juanlugo456/GRUPO-FUNBIO/Talleres/T2/T1 (1).docx

Medición | Valor (V)
1 | 5.063
2 | 5.065
3 | 5.069
4 | 5.070
5 | 5.070
6 | 5.046
7 | 5.018
8 | 5.062
9 | 5.063
10 | 5.027
Promedio | 5.0551
Ea | 0.0551
Er | 0.01102
Medición Valor (V) 1 3.354 2 3.360 3 3.300 4 3.342 5 3.301 6 3.362 7 3.294 8 3.365 9 3.320 10 3.279 Promedio 3.3277 Ea 0.0277 Er 8.39 × 10⁻³ Medición Valor (V) 1 12.03 2 12.05 3 12.02 4 12.07 5 12.00 6 12.04 7 12.03 8 12.06 9 11.99 10 12.06 Promedio 12.035 Ea 0.035 Er 2.92 × 10⁻³

Voltaje Nominal | Promedio Medido (V) | Error Absoluto Medio (Ea) | Error Relativo Medio (Er)
5 V | 5.0551 | 0.0551 | 0.01102
3.3 V | 3.3277 | 0.0277 | 8.39 × 10⁻³
12 V | 12.035 | 0.035 | 2.92 × 10⁻³
