juanlugo456/GRUPO-FUNBIO/Entregable/Entregable 8.pdf

# Entregable 8 - Grupo 3

# Fundamentos de Biodiseño

# Integrantes:

## Juan Carlos Lugo Lorena Mendez Nathalie Huiza Ignacio Pérez Fabio García Jean Neira

2025

## 1.- Diagrama o Esquema Electrónico

## -Actuador:

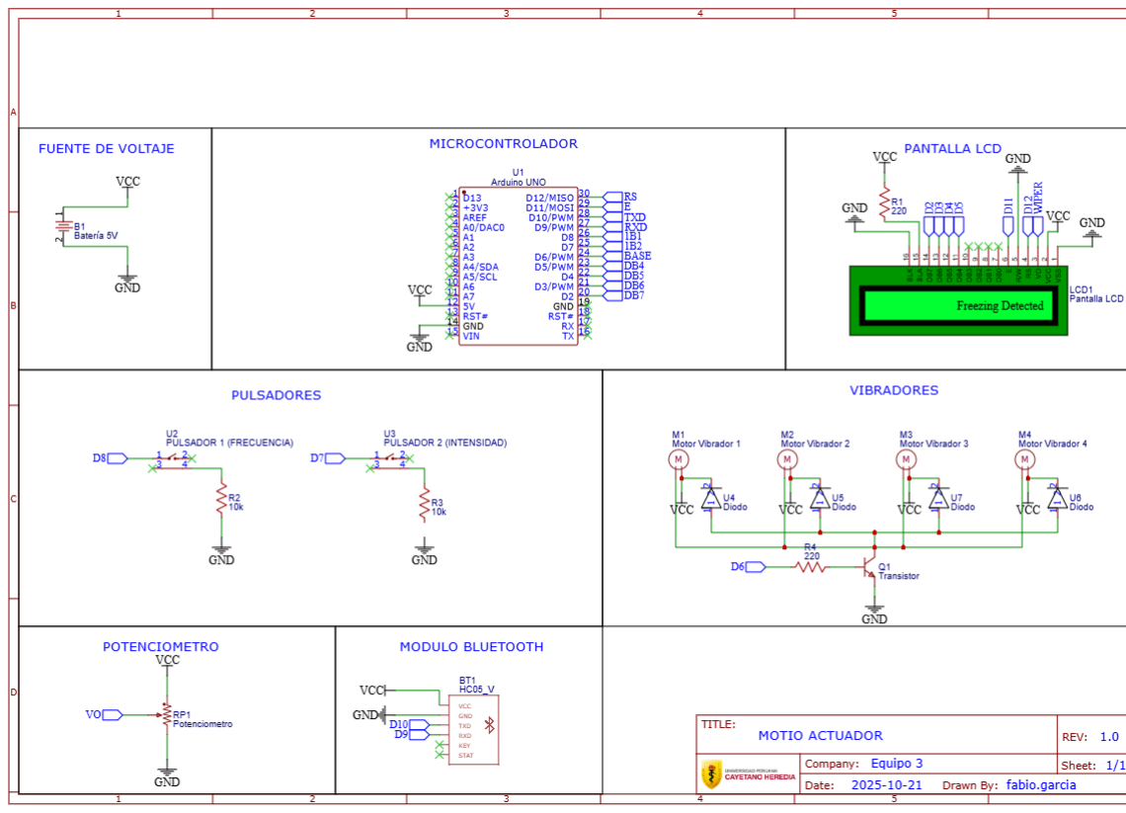
[picture p24: figure]

## -Detector

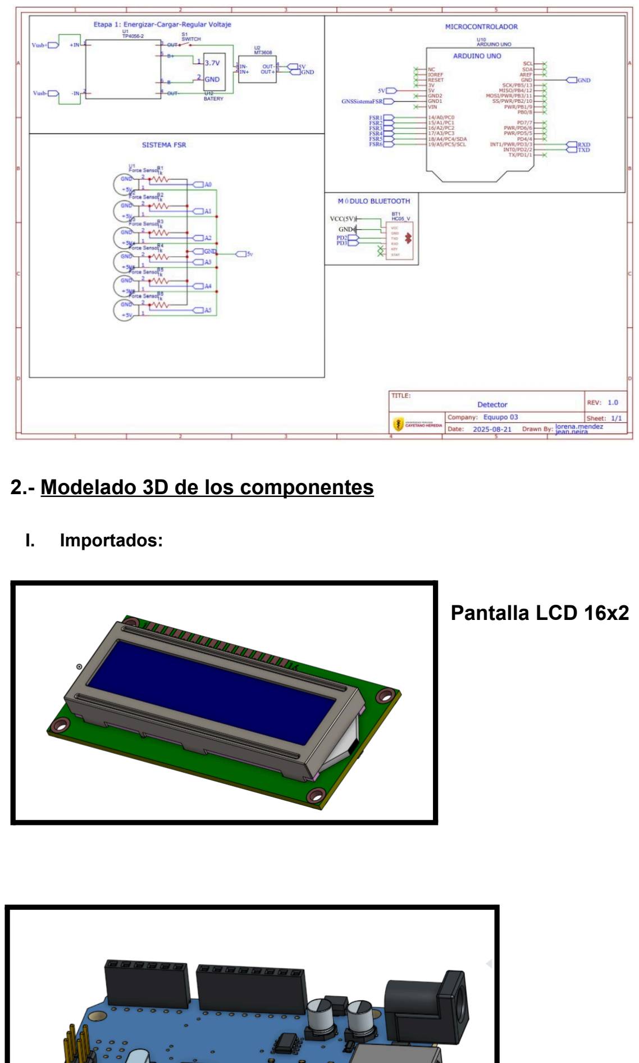
[picture p25: page 3]

## 2.- Modelado 3D de los componentes

I. Importados:

## Pantalla LCD 16x2

## Arduino Uno

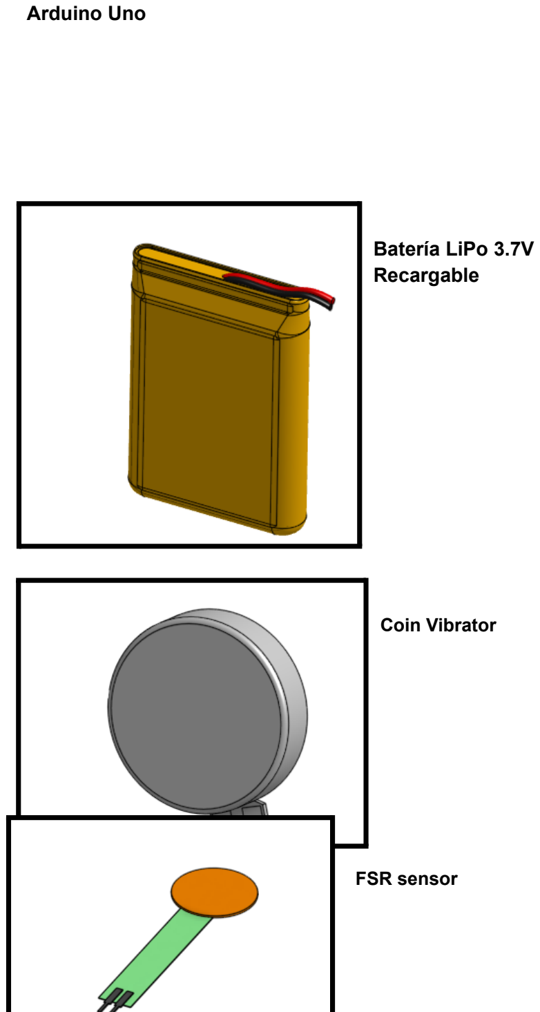
[picture p26: page 4]

## Batería LiPo 3.7V Recargable

### Coin Vibrator

### FSR sensor

## Botón

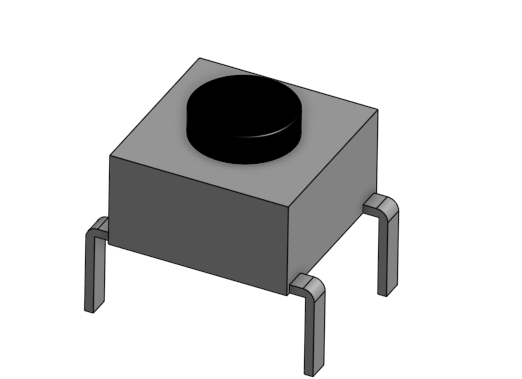
[picture p27: figure]

## II. Modelados:

## Plantilla

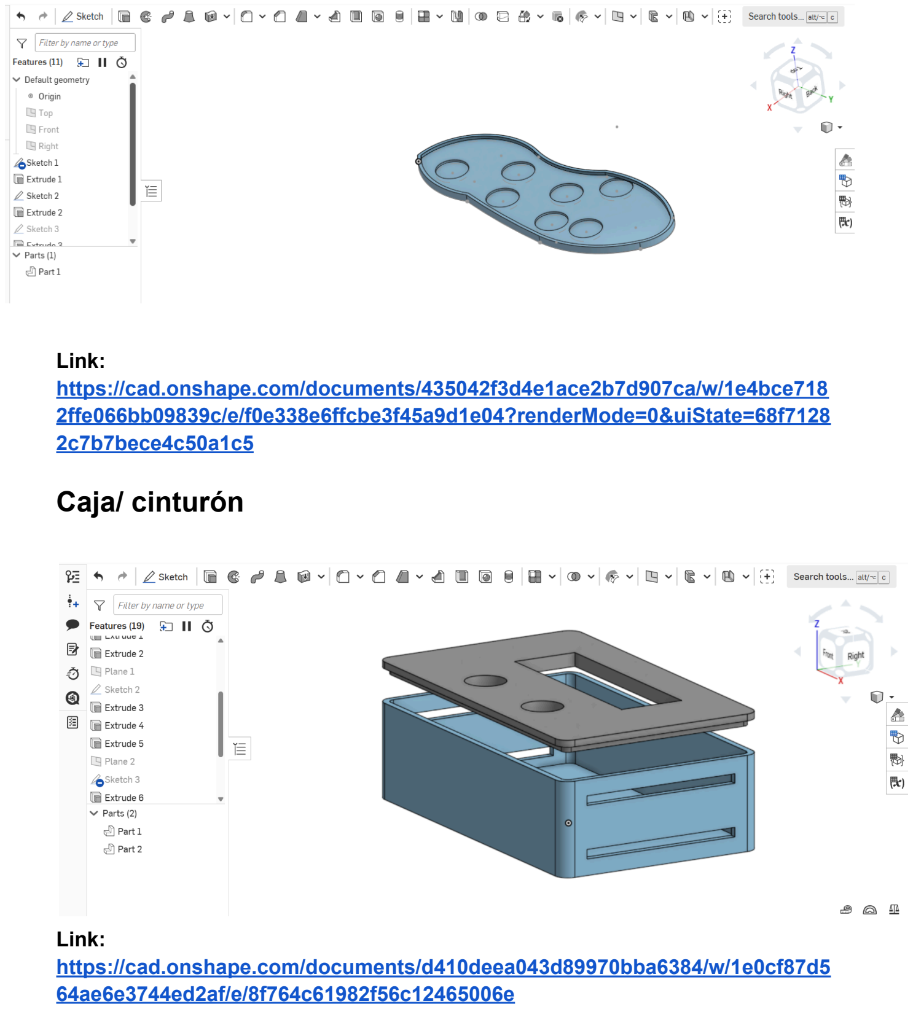
[picture p28: page 6]

Link:
https://cad.onshape.com/documents/435042f3d4e1ace2b7d907ca/w/1e4bce7182ffe066bb09839c/e/f0e338e6ffcbe3f45a9d1e04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 2c7b7bece4c50a1c5 (https://cad.onshape.com/documents/435042f3d4e1ace2b7d907ca/w/1e4bce7182ffe066bb09839c/e/f0e338e6ffcbe3f45a9d1e04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)

## Caja/ cinturón

Link:
https://cad.onshape.com/documents/d410deea043d89970bba6384/w/1e0cf87d564ae6e3744ed2af/e/8f764c61982f56c12465006e (https://cad.onshape.com/documents/d410deea043d89970bba6384/w/1e0cf87d564ae6e3744ed2af/e/8f764c61982f56c12465006e)
