juanlugo456/GRUPO-FUNBIO/Talleres/T8/lorena-mendez-certificate.pdf

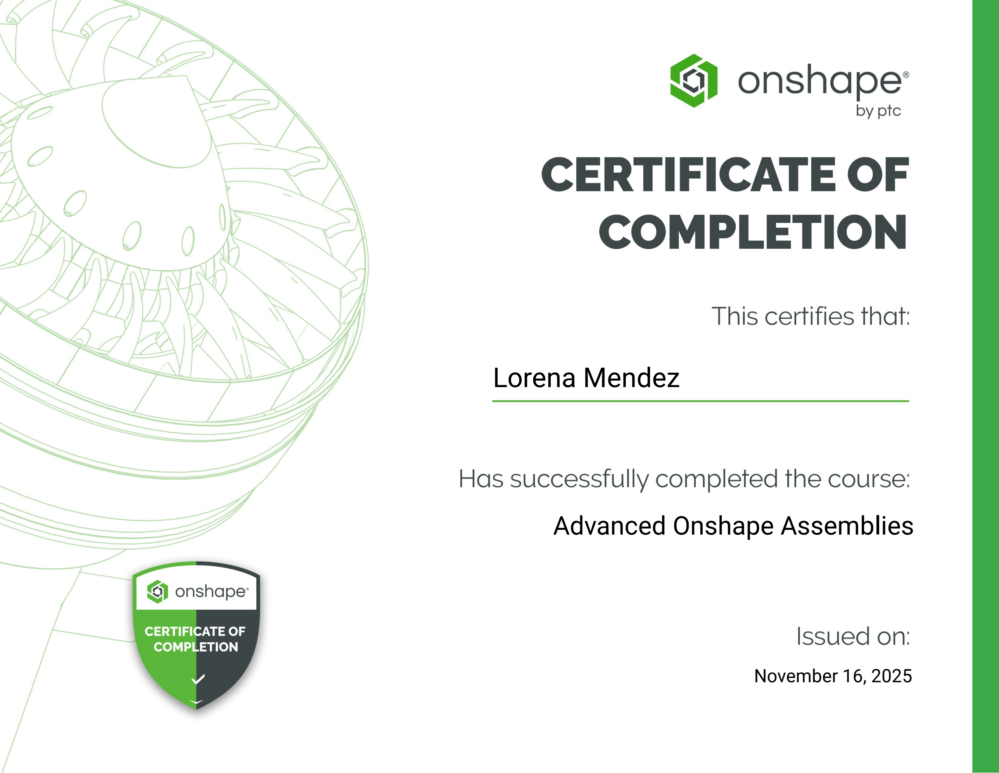
[picture p29: page 1]

Lorena Mendez

Advanced Onshape Assemblies

November 16, 2025
