juanlugo456/GRUPO-FUNBIO/Talleres/T8/Taller 8 certificado Ignacio Pérez.pdf

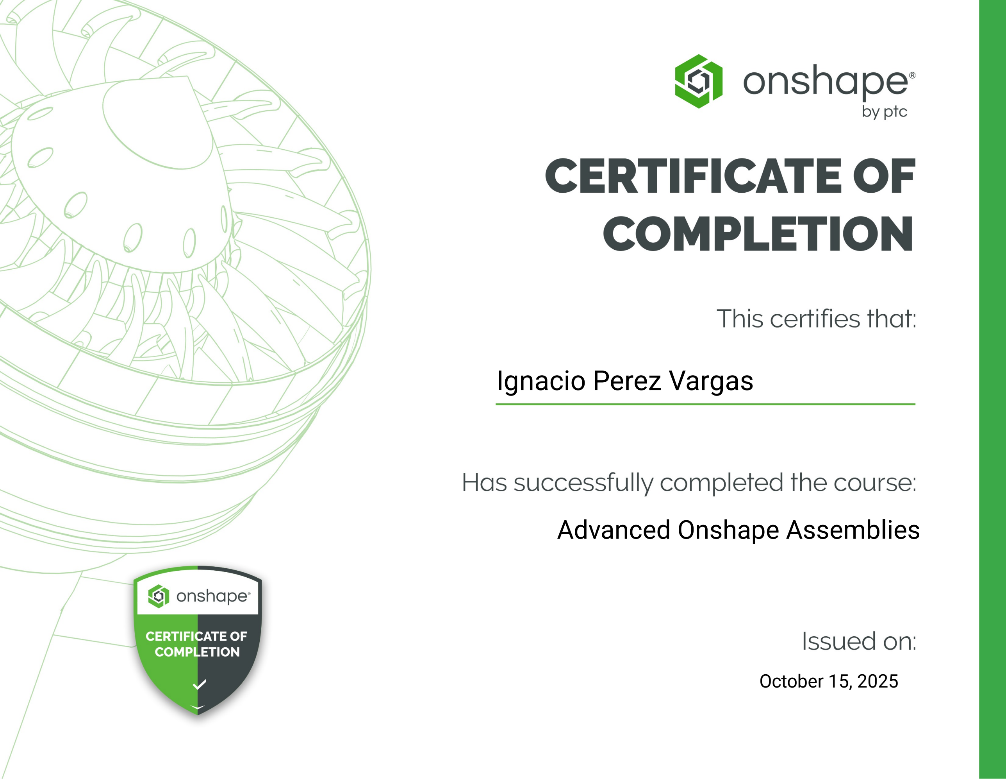
[picture p30: page 1]

Ignacio Perez Vargas

Advanced Onshape Assemblies

October 15, 2025
