juanlugo456/GRUPO-FUNBIO/Talleres/T8/fabio-ivan-garcia-soto-032f19d1-8f02-4be0-8b31-2a58900b8acc-certificate (1).pdf

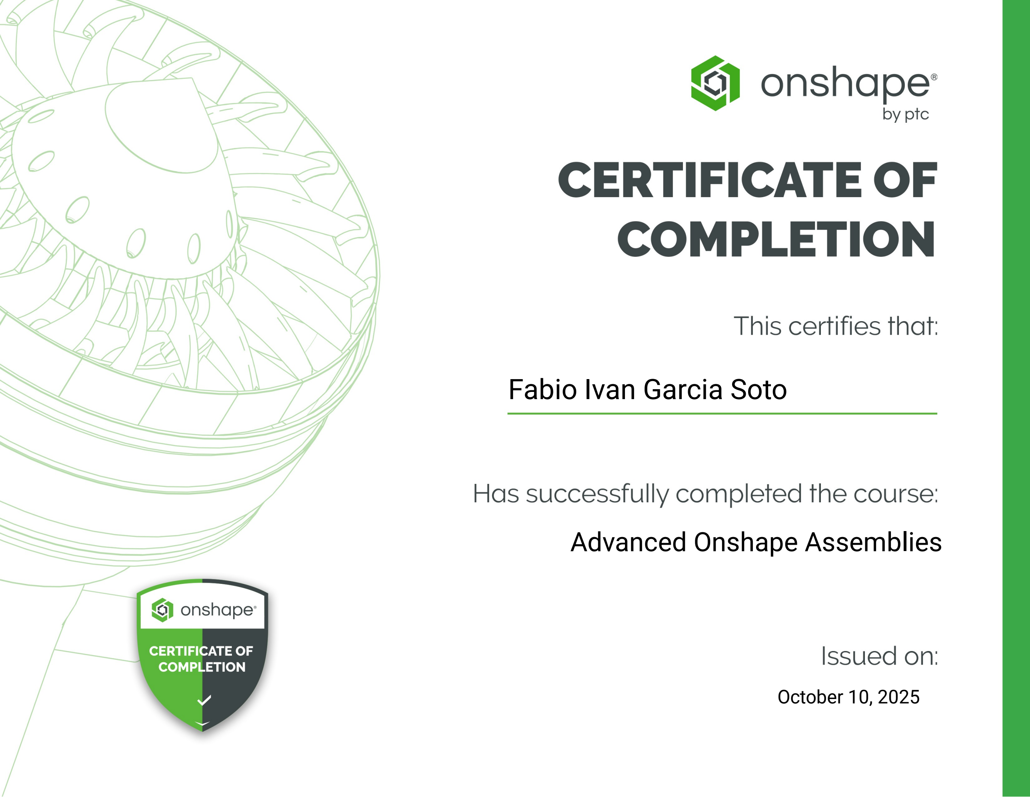
[picture p31: page 1]

Fabio Ivan Garcia Soto

Advanced Onshape Assemblies

October 10, 2025
