juanlugo456/GRUPO-FUNBIO/Talleres/T8/LUGO RODRIGUEZ JUAN CARLOS -taller 8.pdf

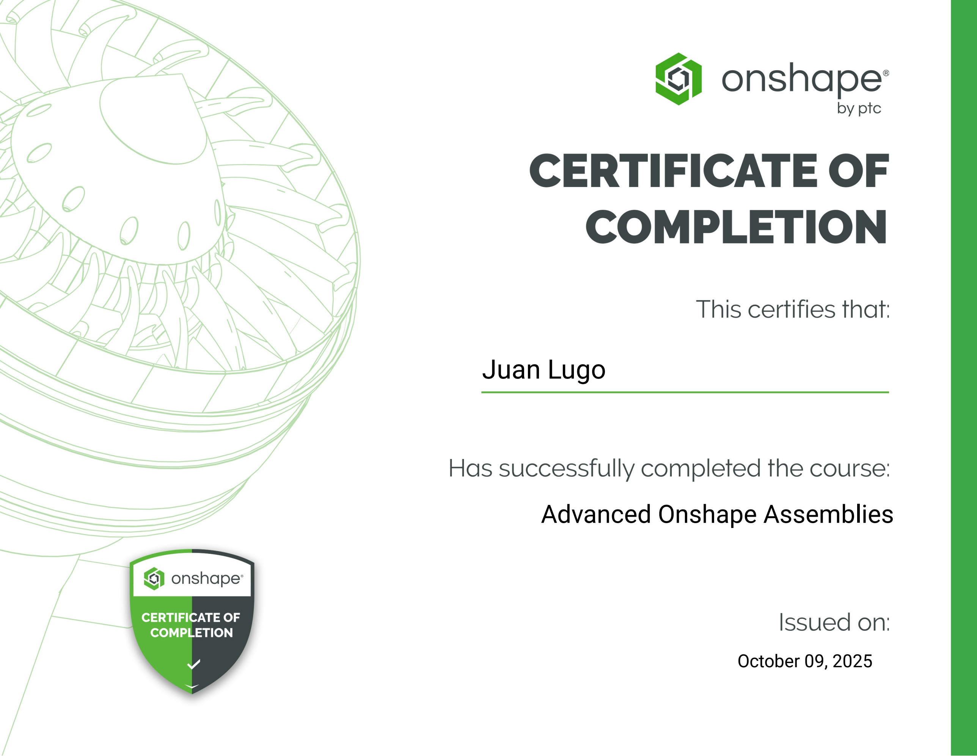
[picture p32: page 1]

Juan Lugo

Advanced Onshape Assemblies

October 09, 2025
