juanlugo456/GRUPO-FUNBIO/Talleres/T8/Nathalie Huiza certificado.pdf

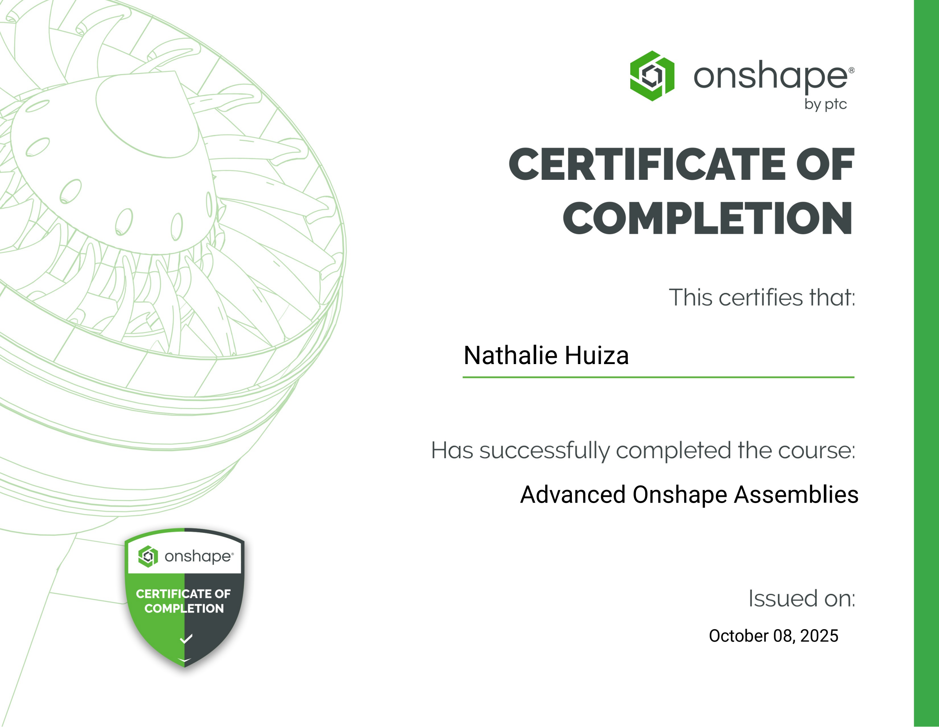
[picture p33: page 1]

Nathalie Huiza

Advanced Onshape Assemblies

October 08, 2025
