juanlugo456/GRUPO-FUNBIO/Talleres/T6/Certificados- Juan Carlos Lugo Rodriguez.pdf

Juan Lugo

September 20, 2025

Onshape Assemblies

Juan Lugo

September 20, 2025

Detailed Drawings

Juan Lugo

September 20, 2025

Multi-Part Part Studios

Juan Lugo

Introduction to Part Studios

September 20, 2025

Juan Lugo

Introduction to Sketching

September 20, 2025
