juanlugo456/GRUPO-FUNBIO/Talleres/T6/Nathalie Antonella Huiza Quispe_C.O.pdf

Nathalie Huiza

Introduction to Sketching

September 17, 2025

Nathalie Huiza

Introduction to Part Studios

September 19, 2025

Nathalie Huiza

September 19, 2025

Multi-Part Part Studios

Nathalie Huiza

September 19, 2025

Onshape Assemblies

Nathalie Huiza

September 19, 2025

Detailed Drawings
