juanlugo456/GRUPO-FUNBIO/Talleres/T2/T2 Resistencias en Protoboard.docx

Pollo

Horizontal

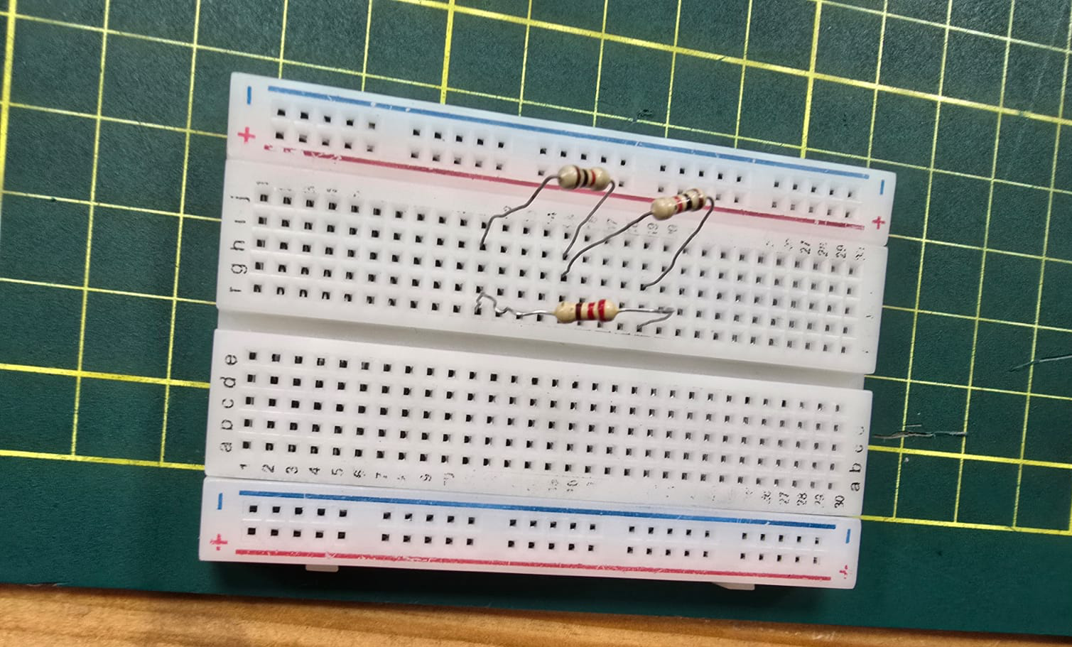
[picture p54: figure]

Vertical

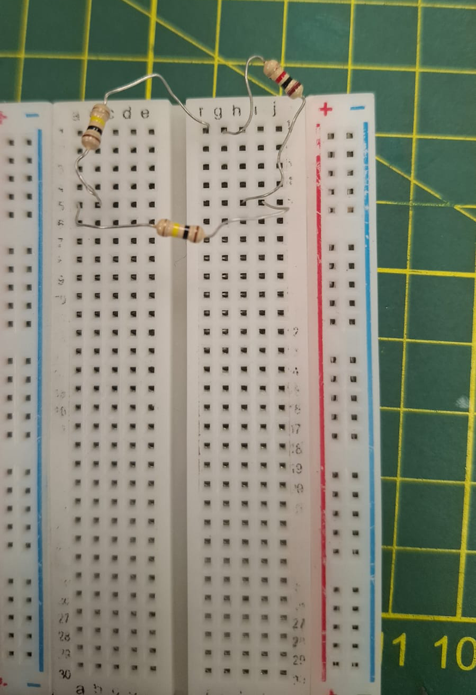
[picture p55: figure]

Gato

Horizontal

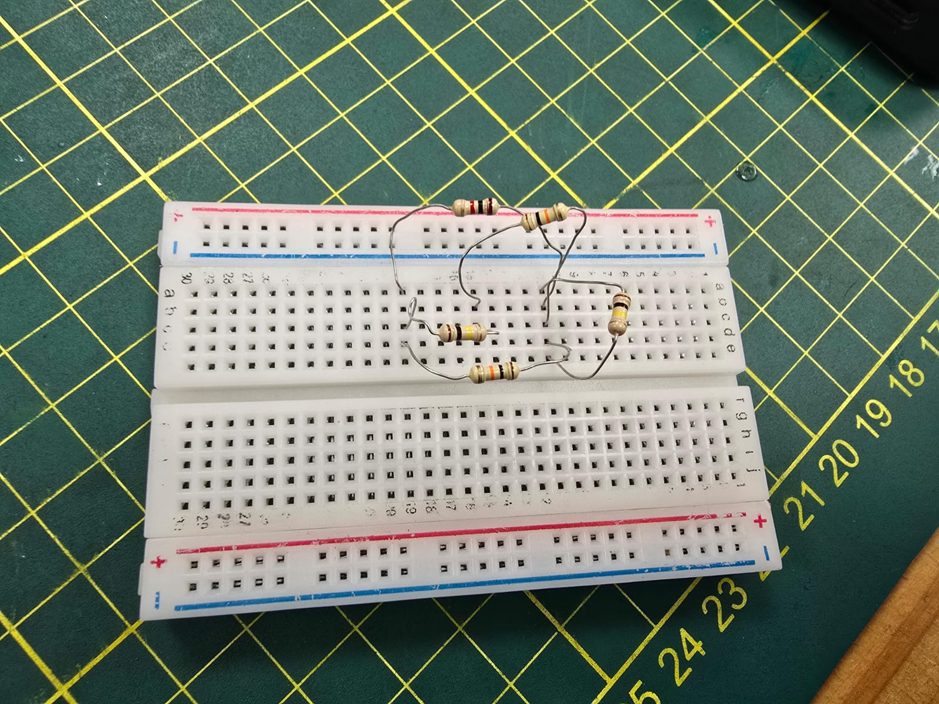
[picture p56: figure]

Vertical

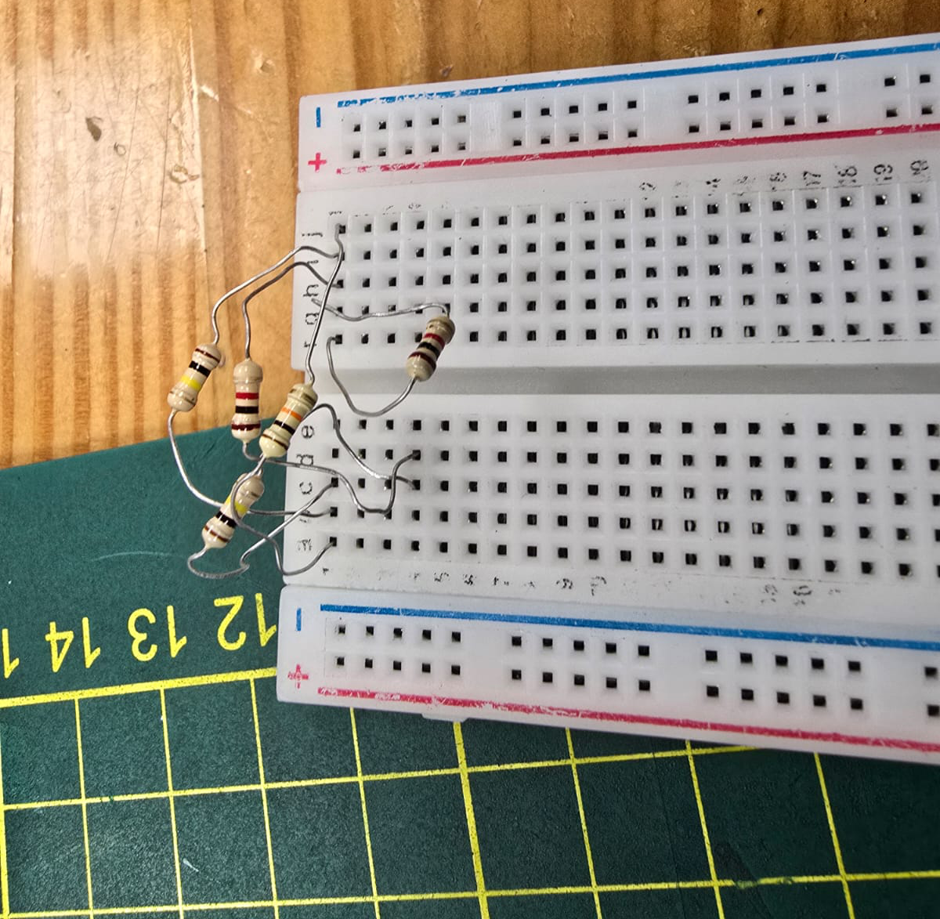
[picture p57: figure]

Dragón

Vertical

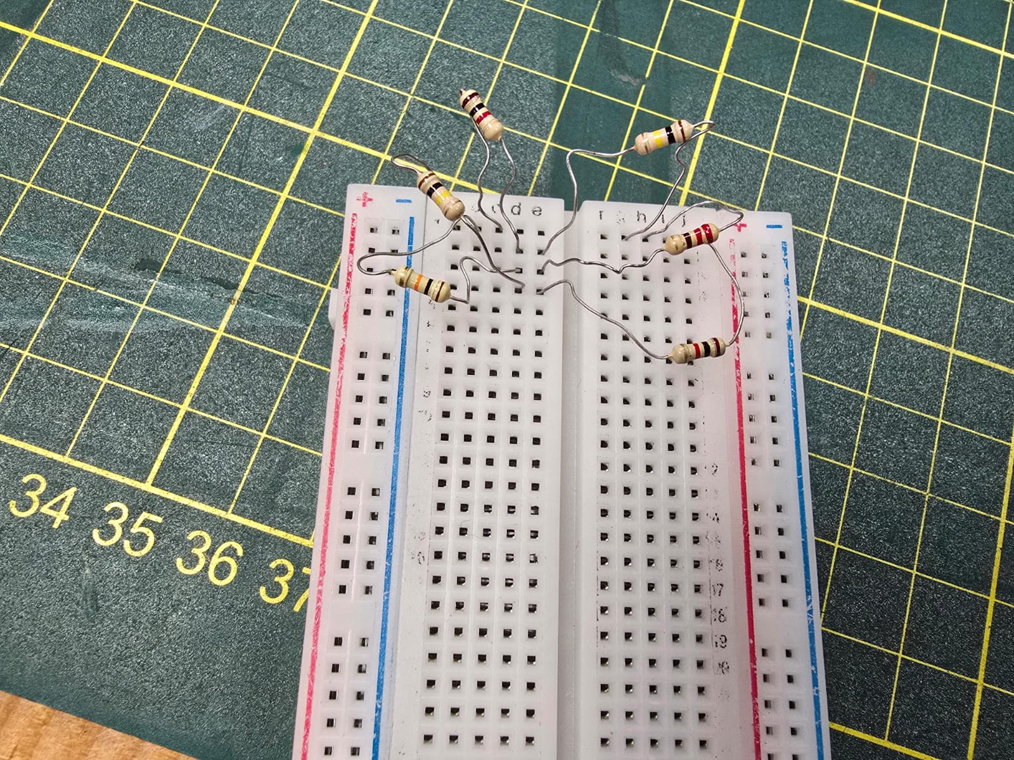
[picture p58: figure]

Horizontal

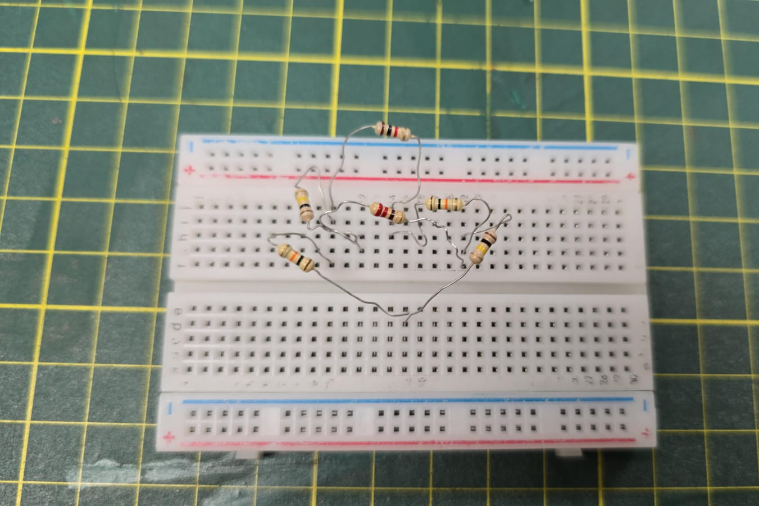
[picture p59: figure]
