juanlugo456/GRUPO-FUNBIO/Talleres/T2/T3 divisor resistivo.docx

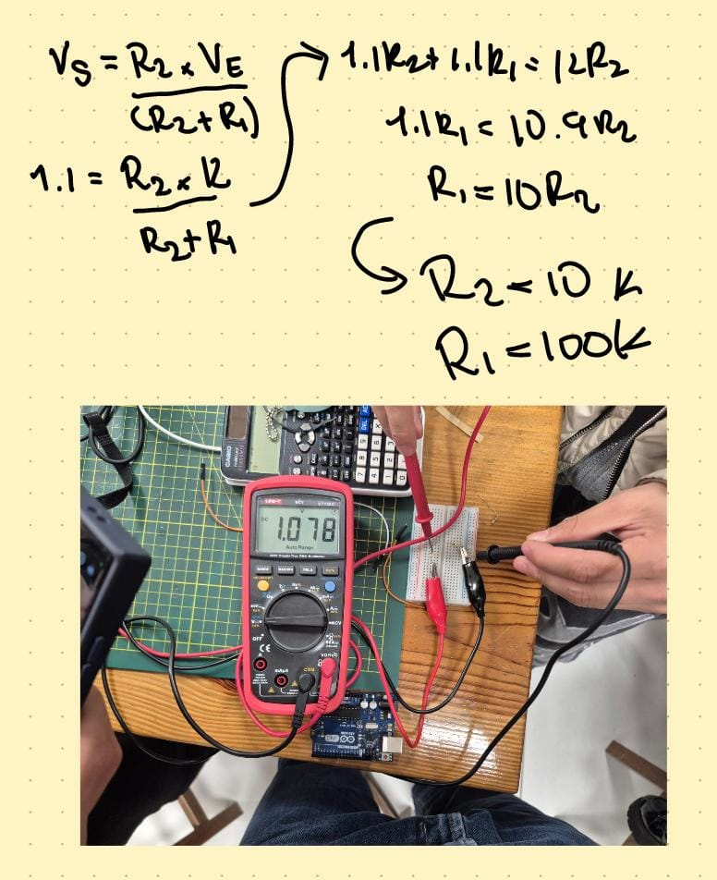
[picture p60: figure]
