juanlugo456/GRUPO-FUNBIO/Documentación/HITO 2 - FUNBIO.pdf

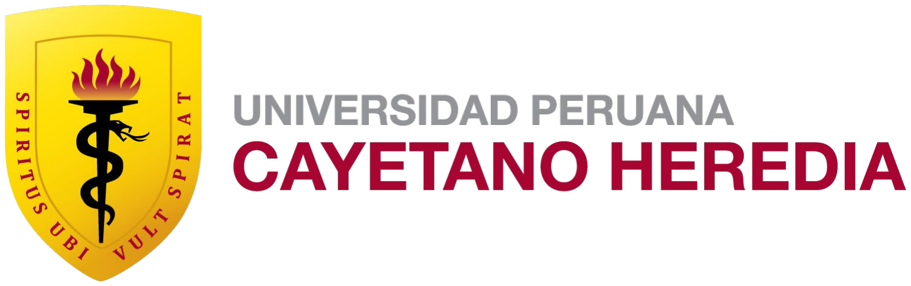
[picture p72: figure]

# MOTIO - Hito 2

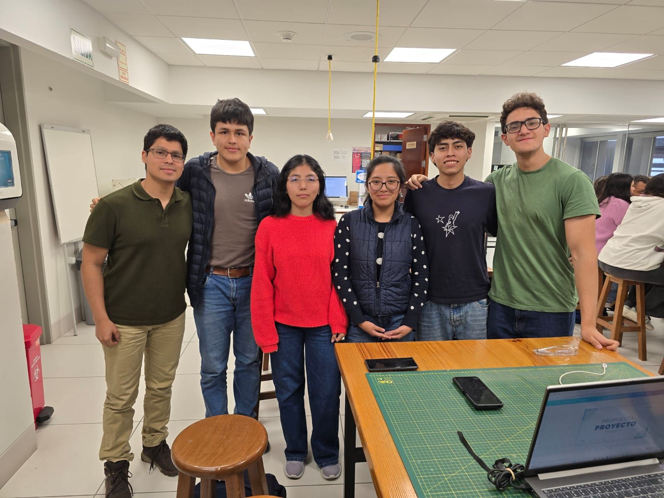
[picture p73: figure]

Integrantes:

Fabio García - Programación y electrónica Juan Carlos Lugo - Coordinador
Ignacio Pérez - Prototipado/ elaboración de entregables
Jean Neira - Electrónica
Lorena Mendez - Electrónica
Nathalie Huiza - Diseño y prototipado/ actualizar información

## Problemática

- El Parkinson causa alteraciones motoras que afectan la marcha y el equilibrio.
- El freezing of gait (FOG) aparece en hasta 60% de los pacientes y aumenta el riesgo de caídas.
- Las soluciones actuales de cueing no detectan FOG en tiempo real.
- Tampoco brindan un estímulo háptico automático, rápido y discreto al instante del bloqueo.
- Existe una brecha tecnológica: integrar detección inmediata + cueing vibratorio inmediato para mejorar movilidad y autonomía.

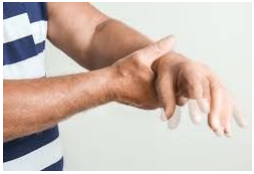
[picture p74: figure]

## Problemática

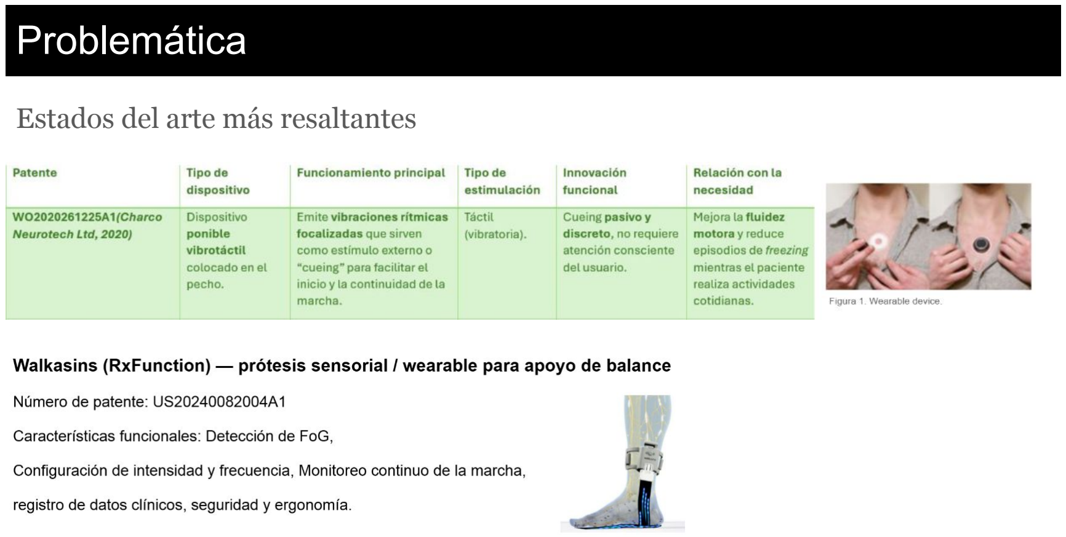
[picture p75: page 3]

Estados del arte más resaltantes

## Solución

### Plantilla inteligente que detecta síntomas de FOG y activa vibraciones ubicadas en el abdomen

Pasos:

1. La plantilla detecta patrones anormales de presión al caminar.
2. El módulo en el cinturón identifica un episodio de FOG.
3. El cinturón envía una vibración inmediata para reiniciar la marcha.

## Tracción

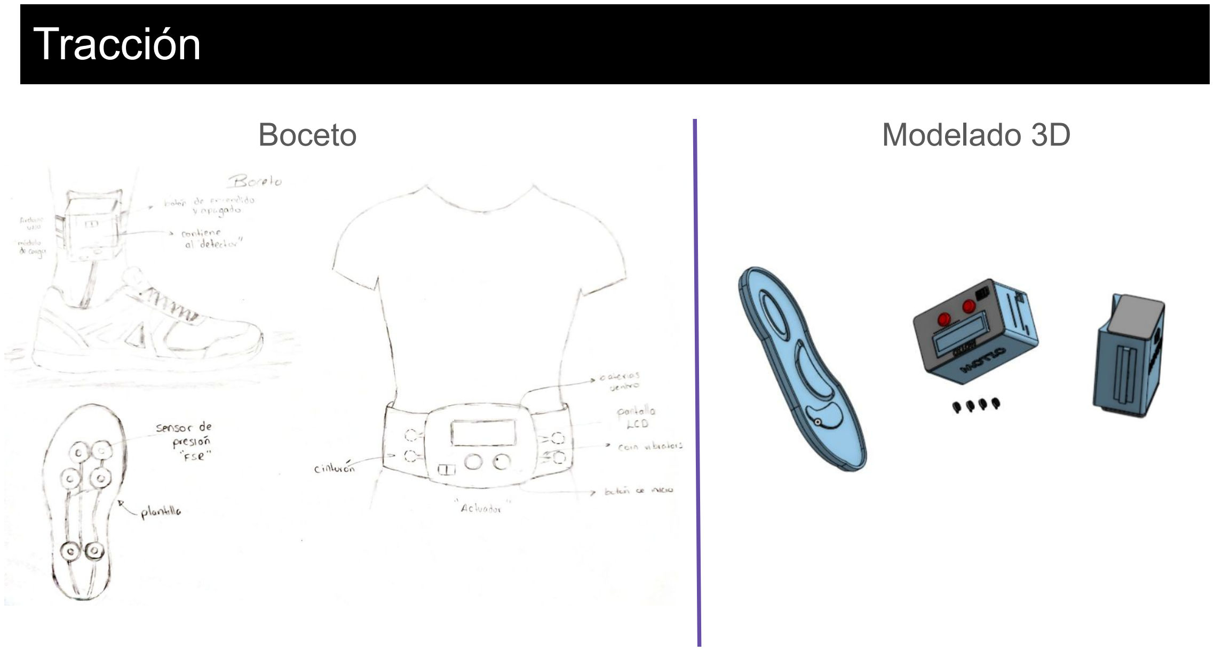
[picture p76: page 5]

Boceto | Modelado 3D

## Diagrama de flujo

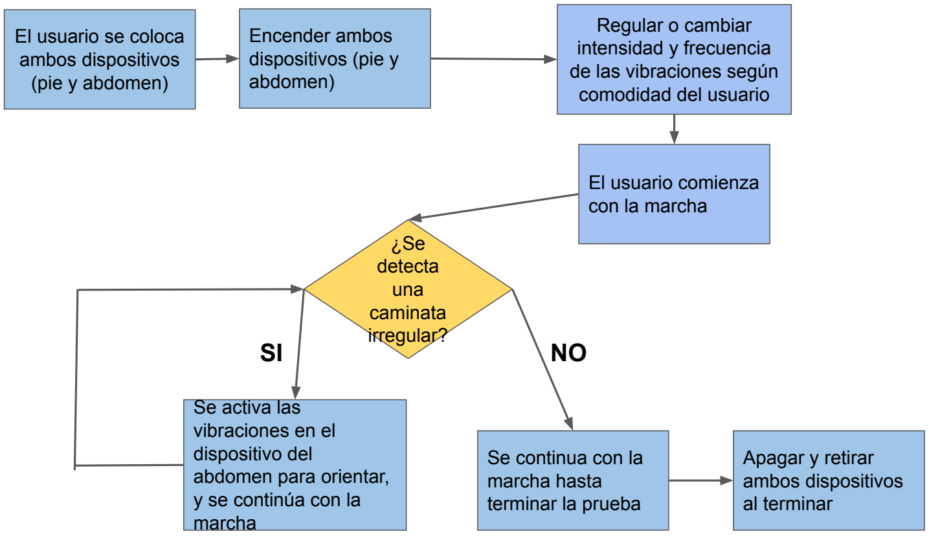
[picture p77: figure]
Encender ambos dispositivos (pie y abdomen); Regular o cambiar intensidad y frecuencia de las vibraciones según comodidad del usuario; El usuario se coloca ambos dispositivos (pie y abdomen); El usuario comienza con la marcha; ¿Se detecta una caminata irregular?; Se continua con la marcha hasta terminar la prueba; Se activa las vibraciones en el dispositivo del abdomen para orientar, y se continúa con la marcha; Apagar y retirar ambos dispositivos al terminar

## Diagramas electrónicos

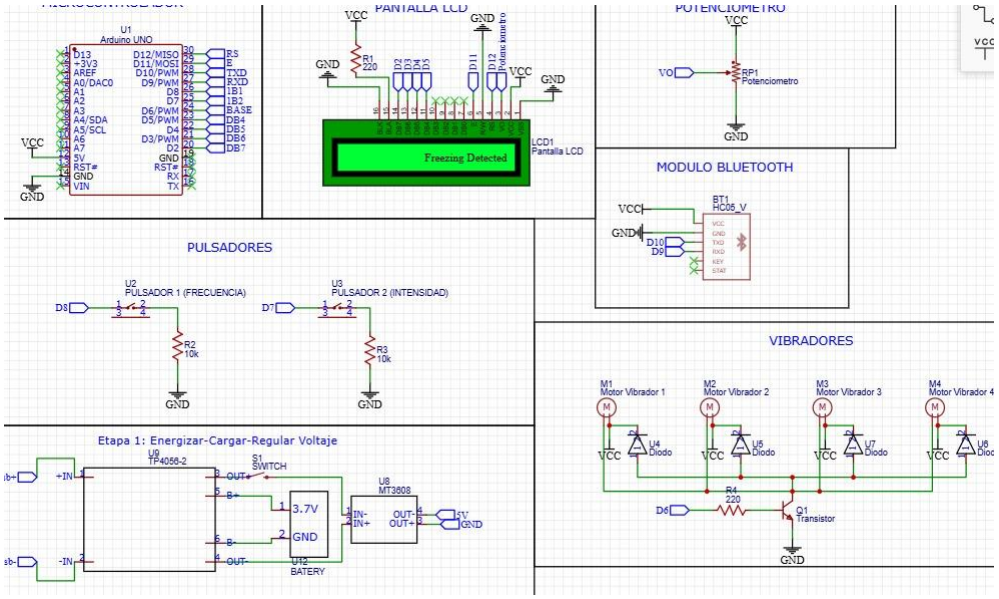
[picture p78: figure]

## Actuador

## Diagramas electrónicos

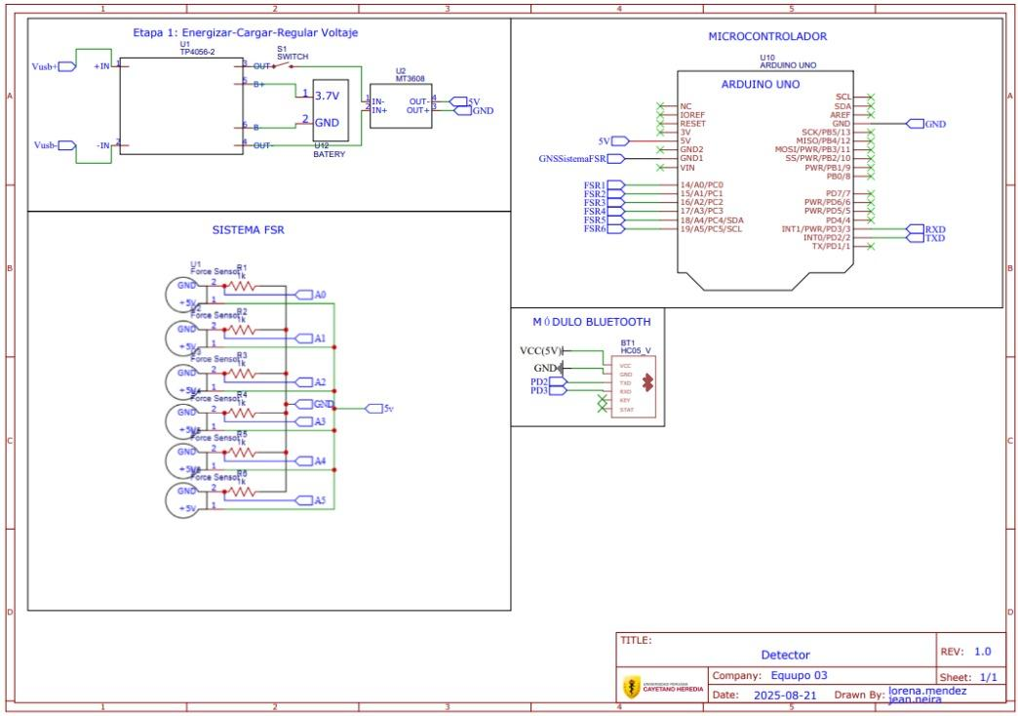
[picture p79: figure]

## Detector

## Manufactura Digital

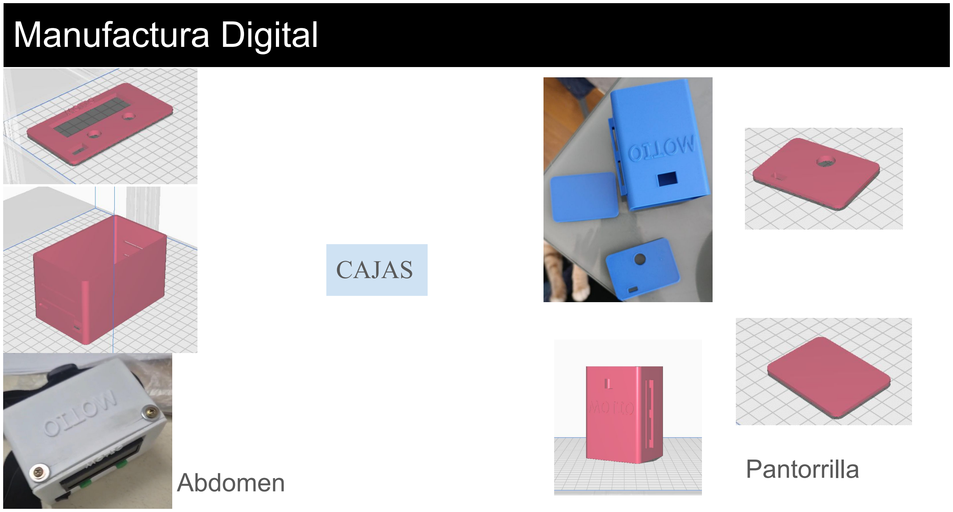
[picture p80: page 9]

CAJAS

Abdomen | Pantorrilla

## Manufactura Digital

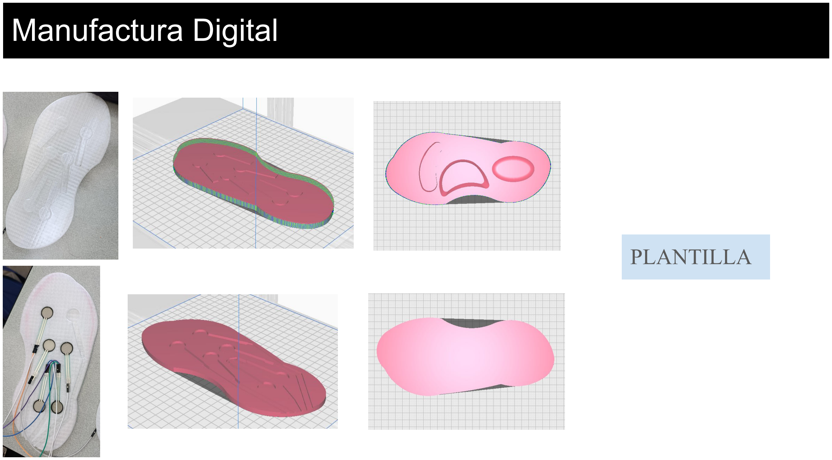
[picture p81: page 10]

PLANTILLA

## Componentes Electrónicos

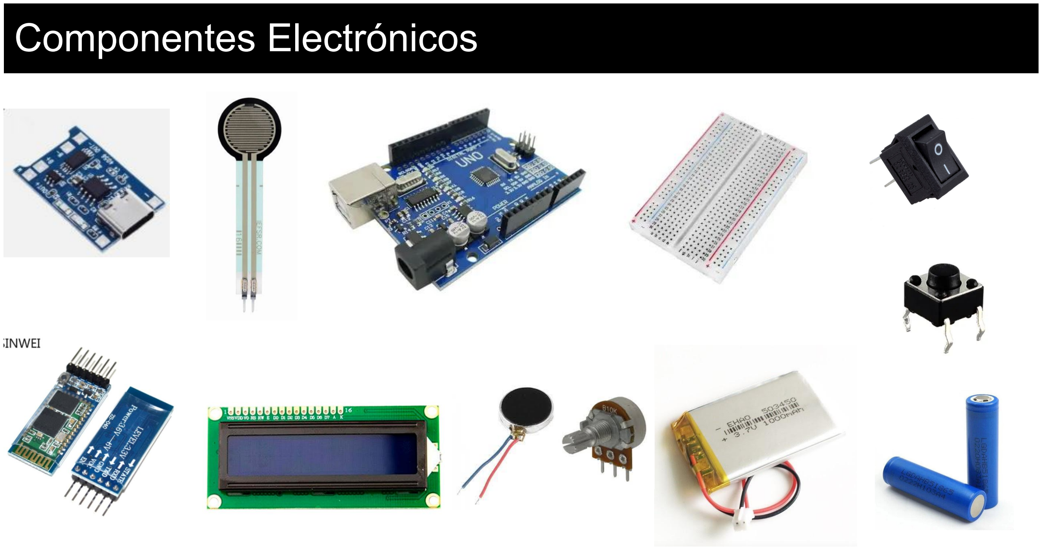
[picture p82: page 11]

## Hardware

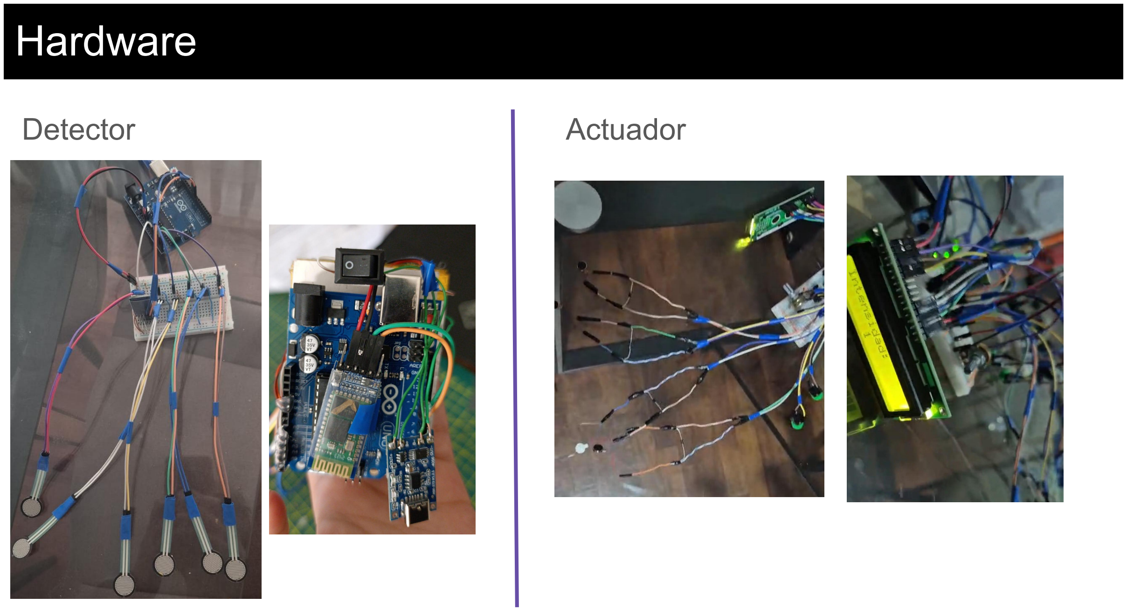
[picture p83: page 12]

Detector | Actuador

Códigos de funcionamiento del detector y actuador

https://github.com/juanlugo456/GRUPO-FUNBIO/blob/5696d07c80632f7c49fbc09b6b840d0a7ff5480c/Entregable/Software%20Hito%202.txt

## Software

Ingresar al Link para ver el código en Github

## Tracción

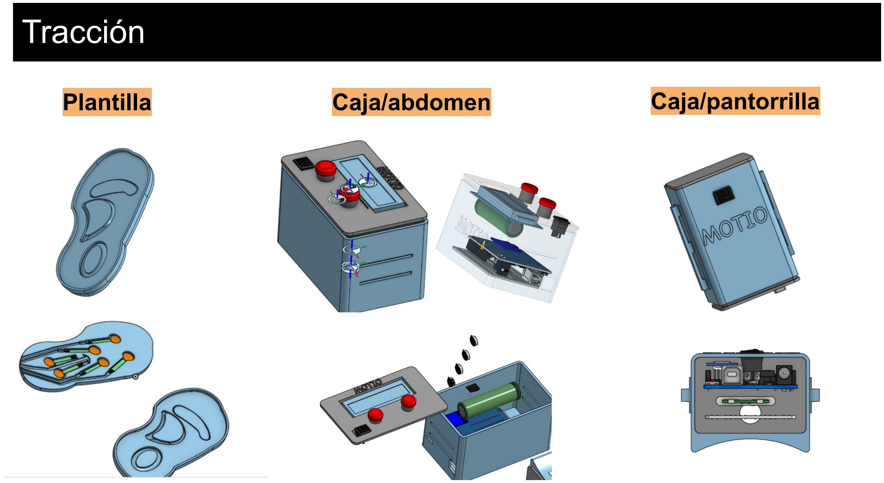
[picture p84: page 14]

Plantilla | Caja/abdomen | Caja/pantorrilla

## Slide extra: Limitaciones

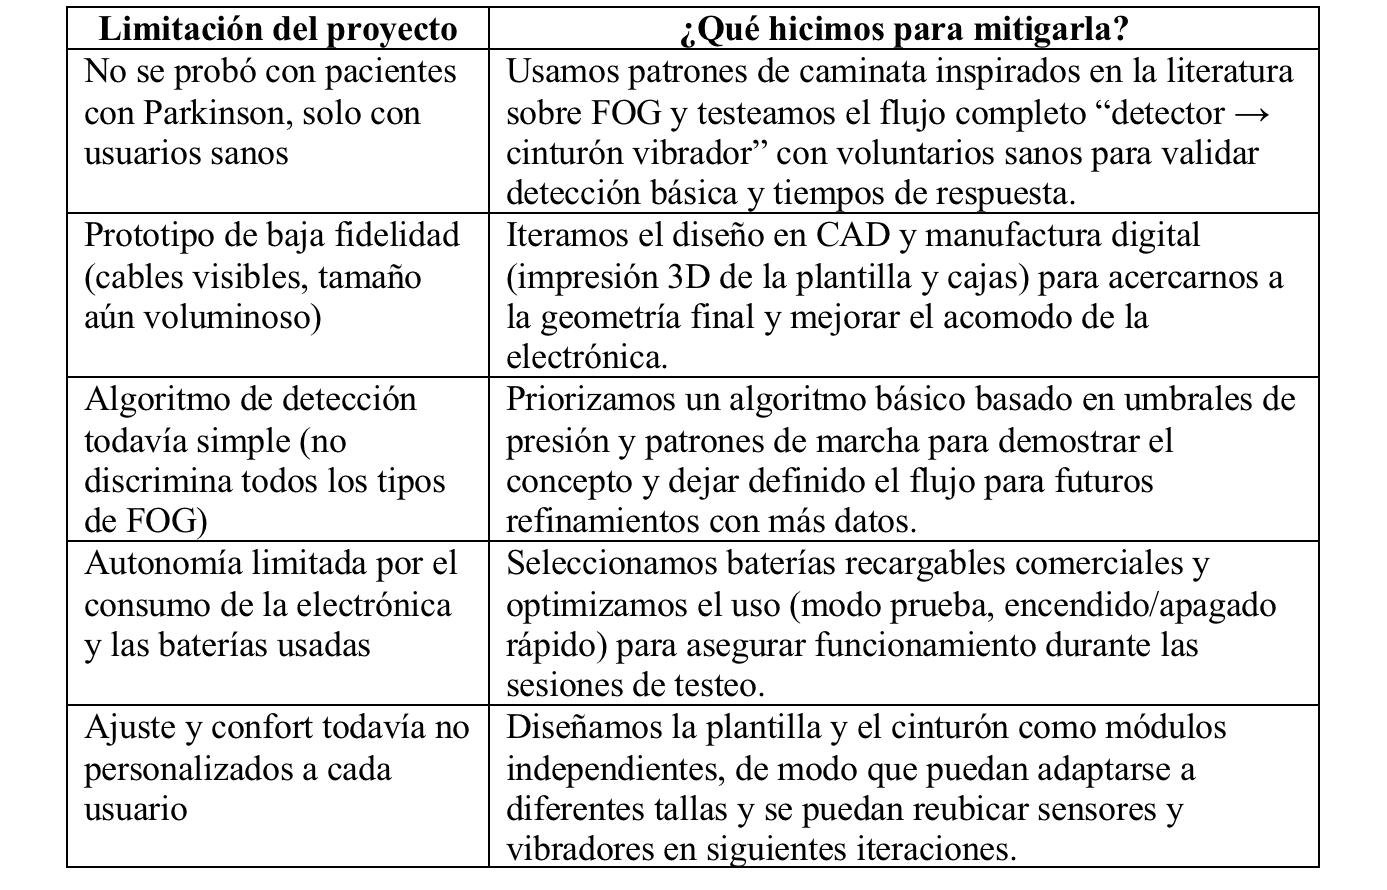
[picture p85: figure]

https://drive.google.com/file/d/1AbwF4mAQ5vQWox3rgK6u8hEFwhtRZYDl/view?usp=drive_link (https://drive.google.com/file/d/1AbwF4mAQ5vQWox3rgK6u8hEFwhtRZYDl/view?usp=drive_link)

## Video del Funcionamiento
