juanlugo456/GRUPO-FUNBIO/Documentación/Hito 1 Grupo 3.pdf

# Motio

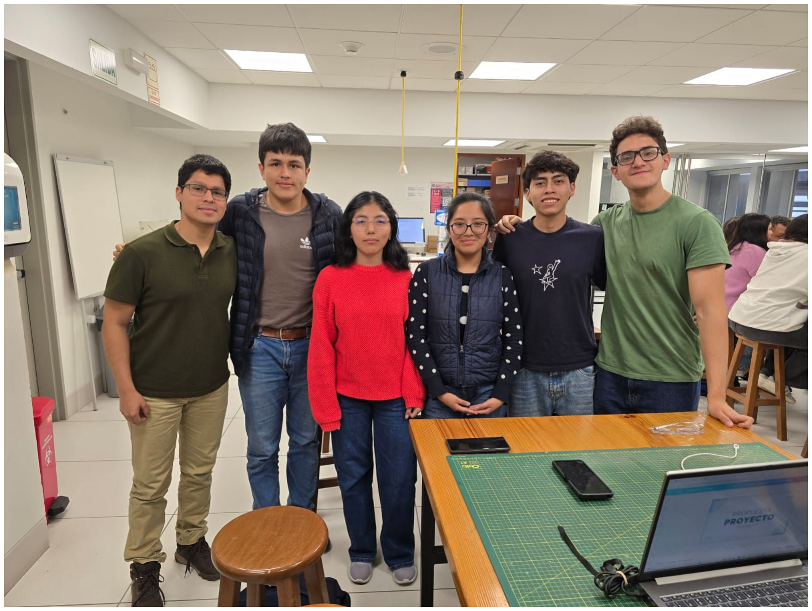
[picture p97: figure]

## Integrantes:

## - Fabio García - Juan Carlos Lugo - Ignacio Pérez - Jean Neira - Lorena Mendez - Nathalie Huiza

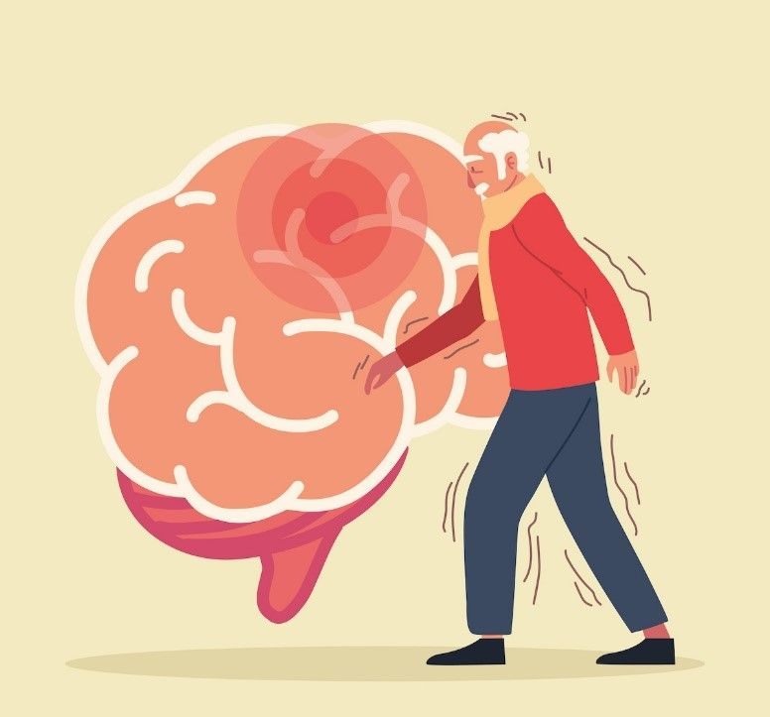
[picture p98: figure]

# Análisis del Caso

## Presentación de la patología:

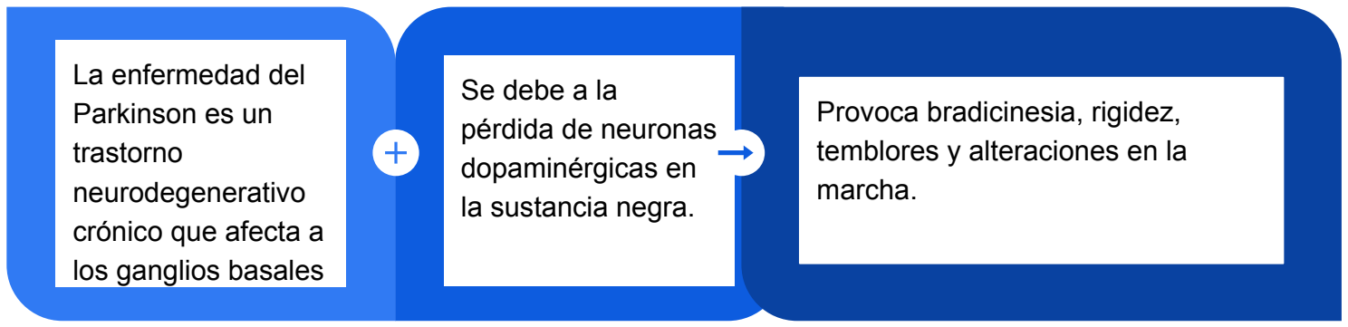
[picture p99: figure]
Se debe a la; pérdida de neuronas; dopaminérgicas en; la sustancia negra.; La enfermedad del; Parkinson es un; trastorno neurodegenerativo crónico que afecta a; los ganglios basales; Provoca bradicinesia, rigidez,; temblores y alteraciones en la; marcha.

# Análisis del Caso

## Dificultad para iniciar y mantener la marcha por

episodios de freezing of gait (FOG).

## Rigidez muscular y bradicinesia que limitan la

movilidad.

Alteraciones del equilibrio y alto riesgo de caídas.

## Conserva funciones cognitivas adecuadas, lo que

permite el uso de ayudas tecnológicas.

## Necesita estimulación sensorial externa (vibratoria o

visual) para recuperar el movimiento.

## Necesidades Funcionales del caso

# Análisis del Caso

Necesidad de mantener una marcha fluida y segura, reduciendo episodios de freezing of gait (FOG).

## El bloqueo al caminar limita actividades básicas como

desplazarse, asearse o salir de casa.

## Enfocarnos en esto ayuda a reducir el riesgo de caídas, la dependencia de terceros y el aislamiento social, además de mejorar su autonomía, confianza al moverse y calidad

de vida diaria.

## Necesidad funcional e impacto en la vida del usuario

# Estado del Arte

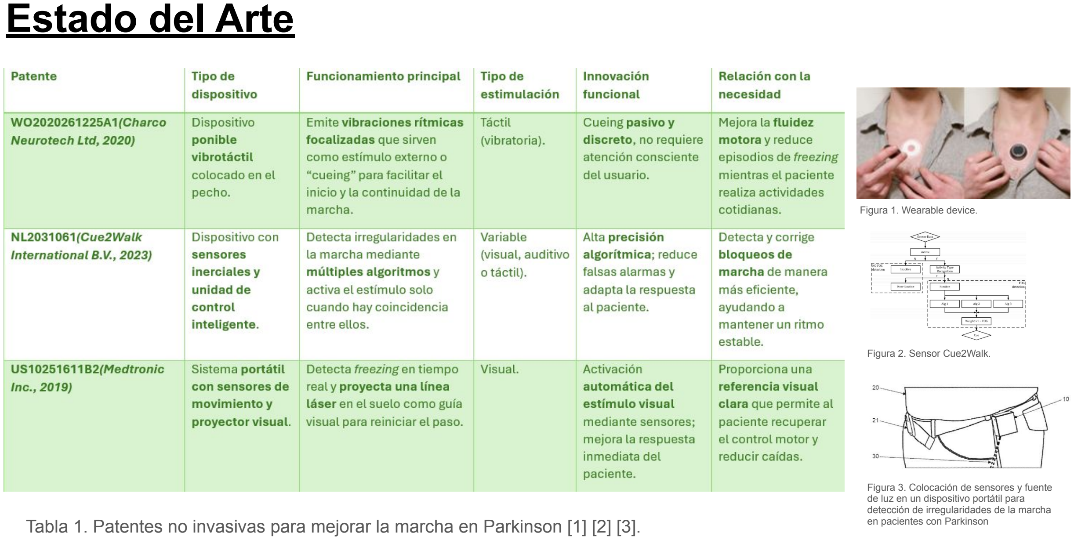
[picture p100: page 5]

Tabla 1. Patentes no invasivas para mejorar la marcha en Parkinson [1] [2] [3].

Figura 1. Wearable device.

Figura 2. Sensor Cue2Walk.

Figura 3. Colocación de sensores y fuente de luz en un dispositivo portátil para detección de irregularidades de la marcha en pacientes con Parkinson

# Estado del Arte

## 1. Walkasins (RxFunction) — prótesis sensorial / wearable para apoyo de balance

### Número de patente: US20240082004A1

Características funcionales: Detección de FoG,

Configuración de intensidad y frecuencia, Monitoreo continuo de la marcha,

registro de datos clínicos, seguridad y ergonomía.

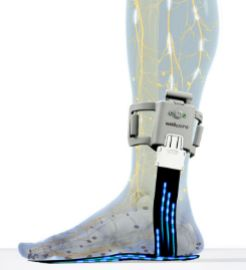
[picture p101: figure]

## 2. U-Step / LaserCane (In-Step Mobility) — bastón/andador con ayuda visual (láser)

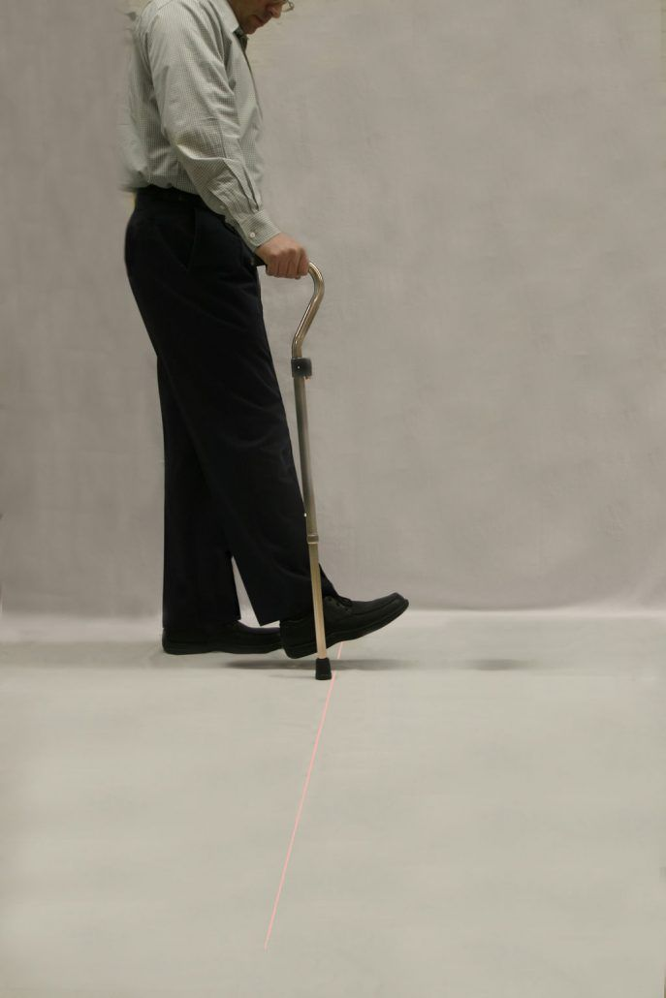
[picture p102: figure]

### Número de patente: US9155675B2

Características funcionales: Láser integrado, Soporte y estabilidad,

Ajustable y ergonómico, Fácil de usar, Portátil y ligero.

# Metodología VDI

## 1. Propuesta a desarrollar:

## - Nuestra propuesta consiste en un sistema wearable compuesto por una plantilla inteligente con sensores de presión(FSR). que se encarga de detectar patrones de movimiento anormales como el freezing of gait en pacientes que padecen Parkinson, y

un cinturón diseñado para emitir estímulos vibrotáctiles en tiempo real con el objetivo de

## mitigar los ya mencionados, episodios de freezing of gait -

# Metodología VDI

## 2. Lista de Requerimientos

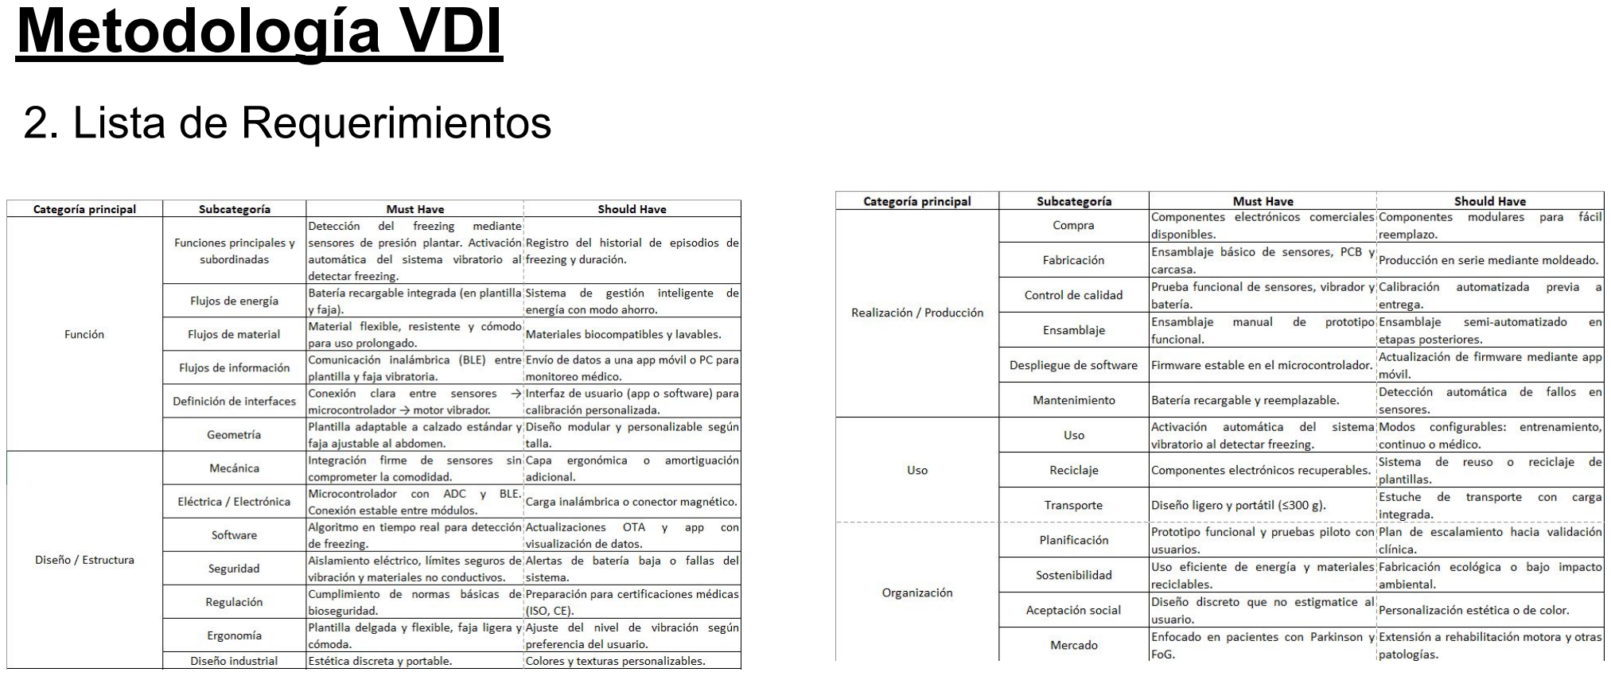
[picture p103: page 8]

# Metodología VDI

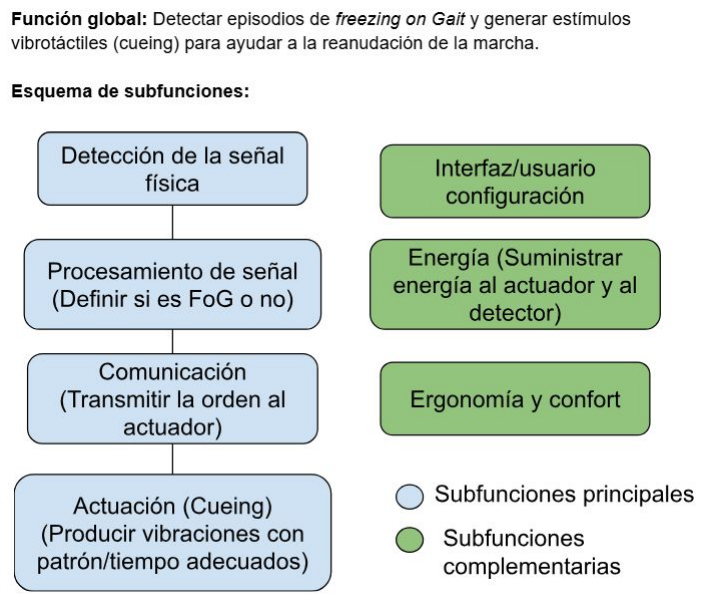
[picture p104: figure]

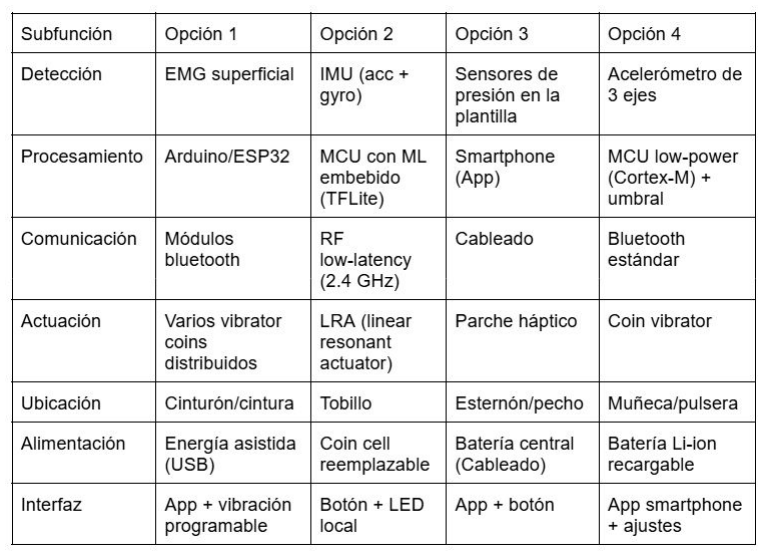
[picture p105: figure]

## Matriz morfológica

# Metodología VDI

## Posibles

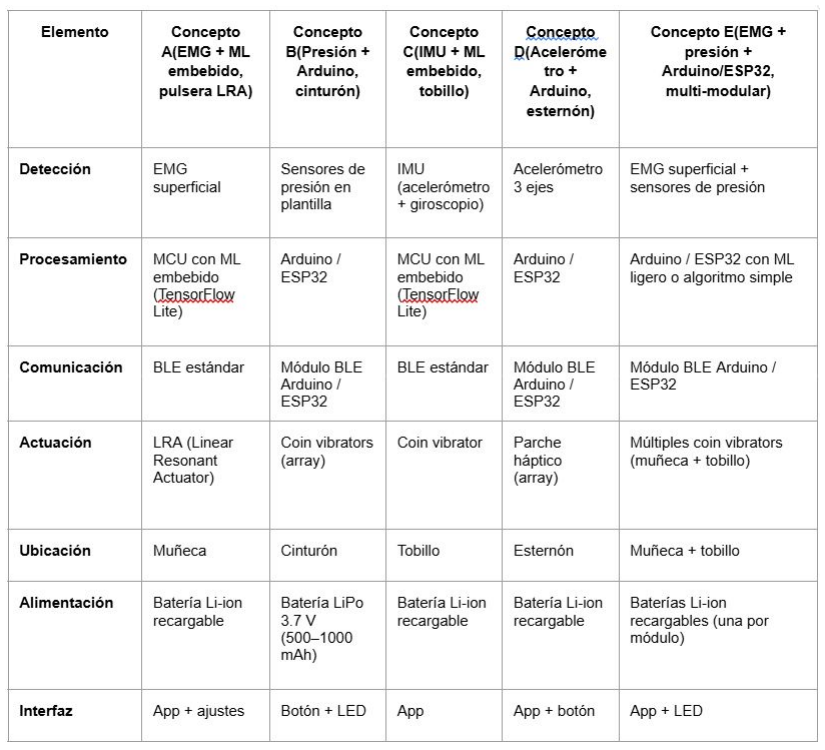
[picture p106: figure]

## combinaciones

## Tabla de evaluación

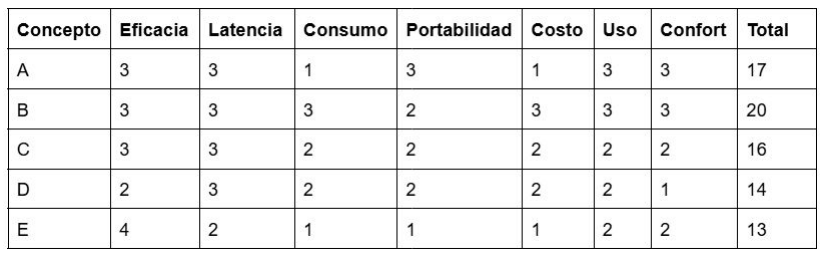
[picture p107: figure]

## A partir de la tabla de evaluación podemos observar que el concepto ganador resulta ser el B, por lo que trabajaremos con este concepto en adelante

# Metodología VDI

## Se presentará 2 bocetos desarrollados basados en el

concepto de solución encontrado.

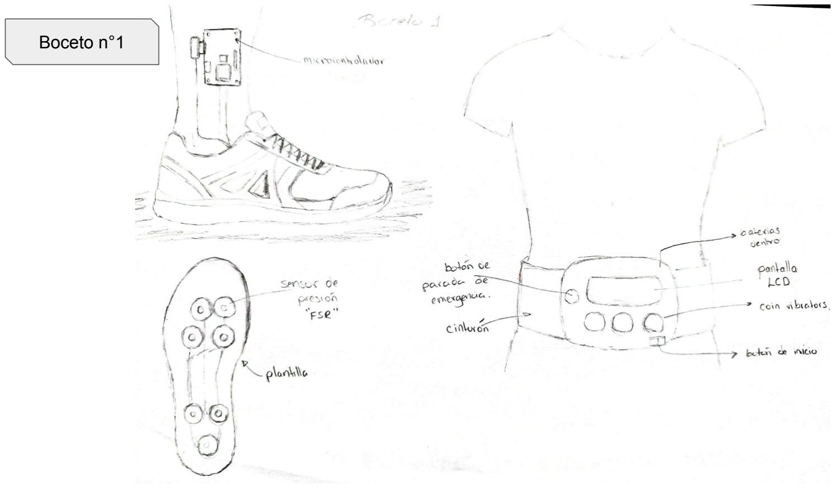
[picture p108: page 14]

### Boceto n°1

## Lista de despiece/ Boceto n°1

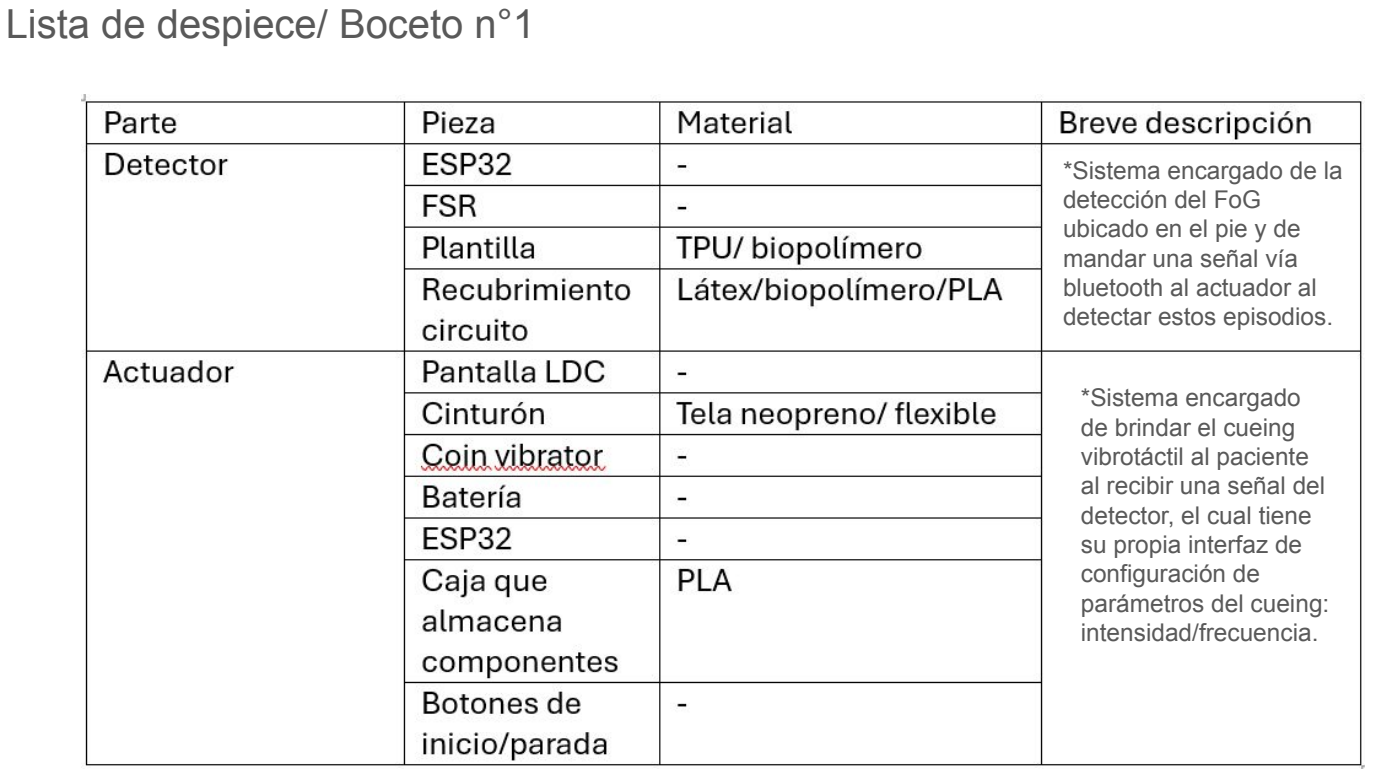
[picture p109: page 15]

*Sistema encargado
de brindar el cueing
vibrotáctil al paciente
al recibir una señal del
detector, el cual tiene
su propia interfaz de
configuración de
parámetros del cueing:
intensidad/frecuencia.

*Sistema encargado de la
detección del FoG
ubicado en el pie y de
mandar una señal vía
bluetooth al actuador al
detectar estos episodios.

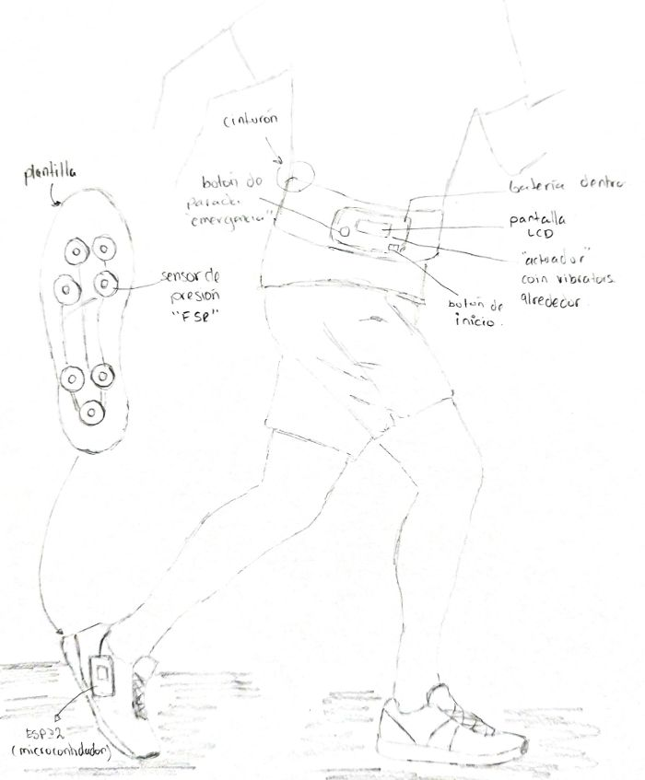
[picture p110: figure]

### Boceto n°2

## Lista de despiece/ Boceto n° 2

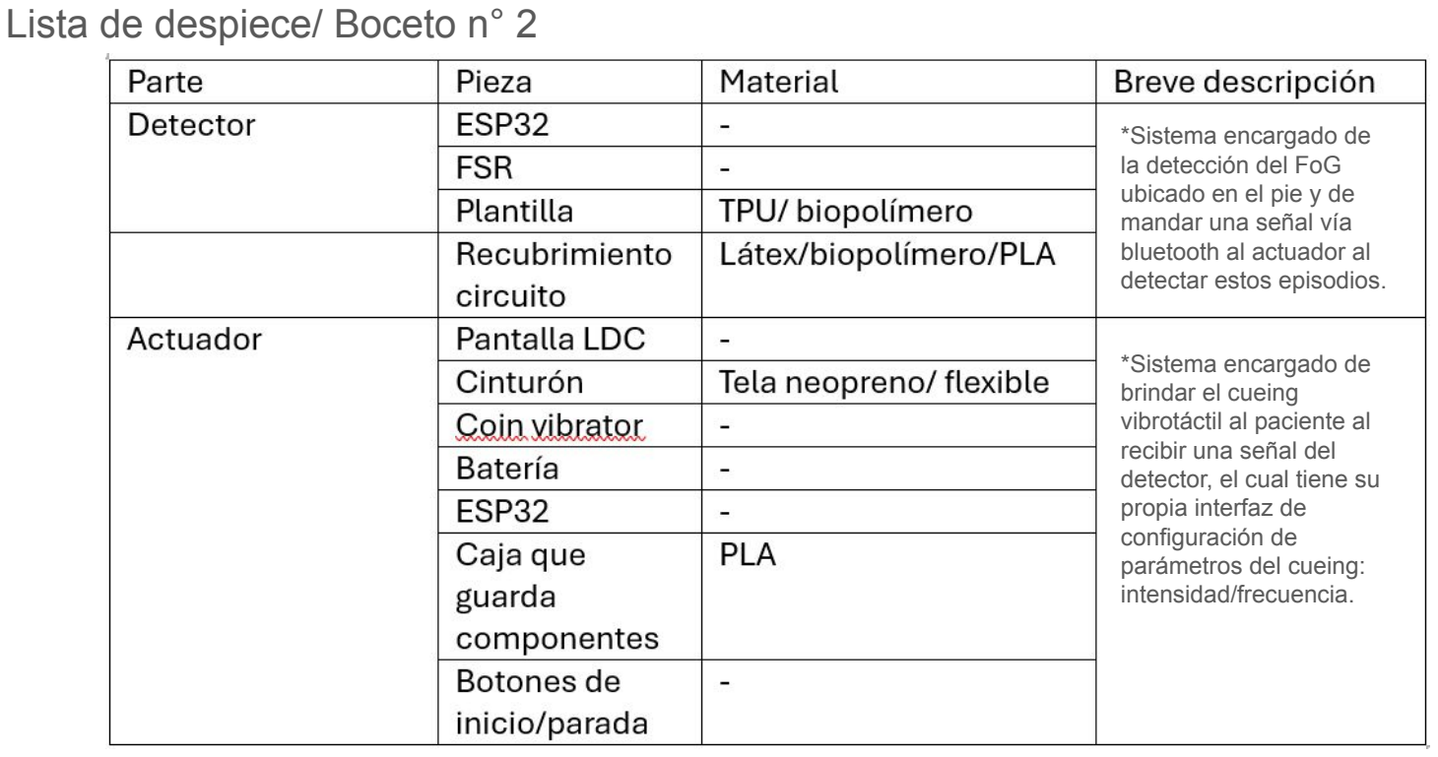
[picture p111: page 17]

*Sistema encargado de
la detección del FoG
ubicado en el pie y de
mandar una señal vía
bluetooth al actuador al
detectar estos episodios.

*Sistema encargado de
brindar el cueing
vibrotáctil al paciente al recibir una señal del
detector, el cual tiene su propia interfaz de
configuración de
parámetros del cueing:
intensidad/frecuencia.

# Conclusiones/siguientes pasos

### Conclusiones:

- El prototipo aborda el freezing of gait con cueing vibrotáctil no invasivo, mejorando la autonomía del paciente.
- Los sensores de presión (FSR) y el procesamiento con ESP32 BLE permiten detección automática y adaptativa.
- Se prioriza bajo costo, portabilidad y confort, cumpliendo los objetivos técnicos del proyecto.
- El índice de anomalía relativa (IAR) ofrece una detección precisa y personalizable.

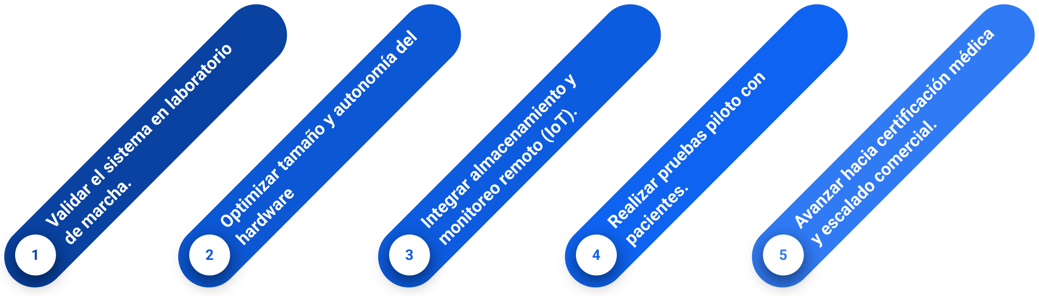
[picture p112: figure]
Avanzar hacia certificación médica; y escalado comercial.; Realizar pruebas piloto con; pacientes.; Integrar almacenamiento y; monitoreo remoto (IoT).; Optimizar tamaño y autonomía del; hardware; Validar el sistema en laboratorio; de marcha.

# Referencias

[1] Charco Neurotech Ltd., Wearable device, WO2020261225A1, World Intellectual Property Organization, 2020. [En línea]. Disponible en: https://patentscope.wipo.int/search/en/detail.jsf?docId=WO2020261225A1
[2] Cue2Walk International B.V., Multiple algorithms for controlling a cueing device, NL2031061, Netherlands Patent Office, 2023. [En línea]. Disponible en: https://patentscope.wipo.int/search/en/detail.jsf?docId=NL2031061
[3] Medtronic Inc., Freezing of gait cue apparatus, US10251611B2, United States Patent and Trademark Office, 2019. [En línea]. Disponible en: https://patents.google.com/patent/US10251611B2/en
[4] RxFunction, Inc., "Clinical Research – Healthcare Professionals," [En línea]. Disponible en: https://rxfunction.com/healthcare-professionals/clinical-research/.
[5] UStep, "LaserCane," [En línea]. Disponible en: https://www.ustep.com/product/lasercane/.
