juanlugo456/GRUPO-FUNBIO/Talleres/T8/Certificado taller 8 Ignacio Pérez Vargas.pdf

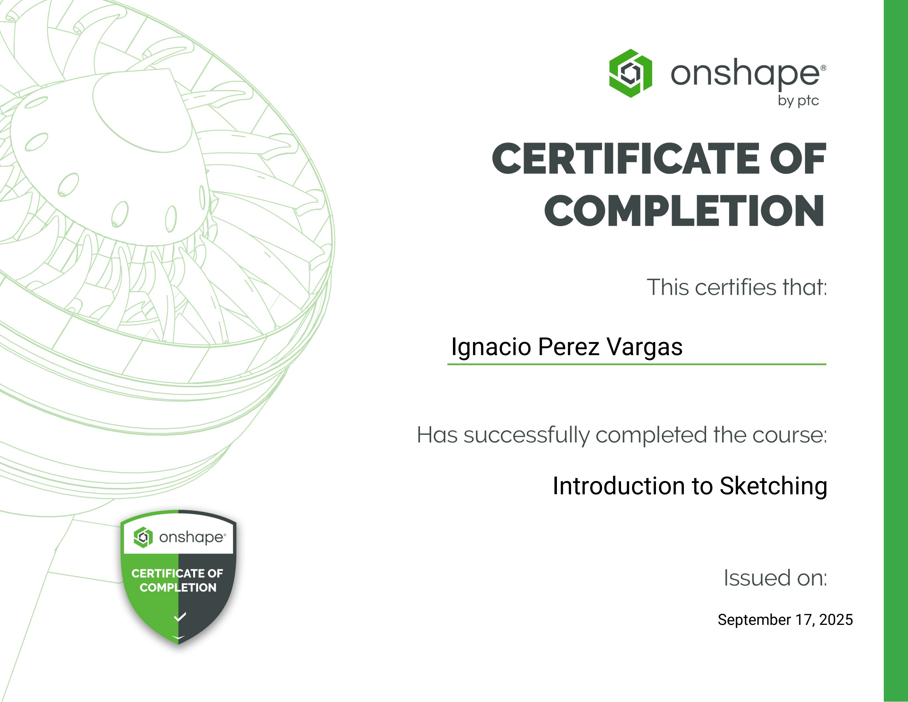
[picture p113: page 1]

Ignacio Perez Vargas

Introduction to Sketching

September 17, 2025
