juanlugo456/GRUPO-FUNBIO/Talleres/T8/Lorena Mendez S._Taller 8.pdf

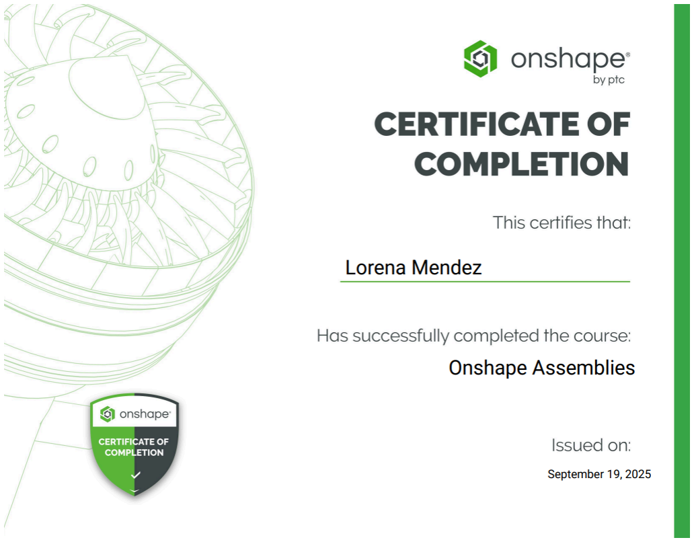
[picture p114: figure]
