juanlugo456/GRUPO-FUNBIO/Talleres/T6/Onshape Lorena Mendez.pdf

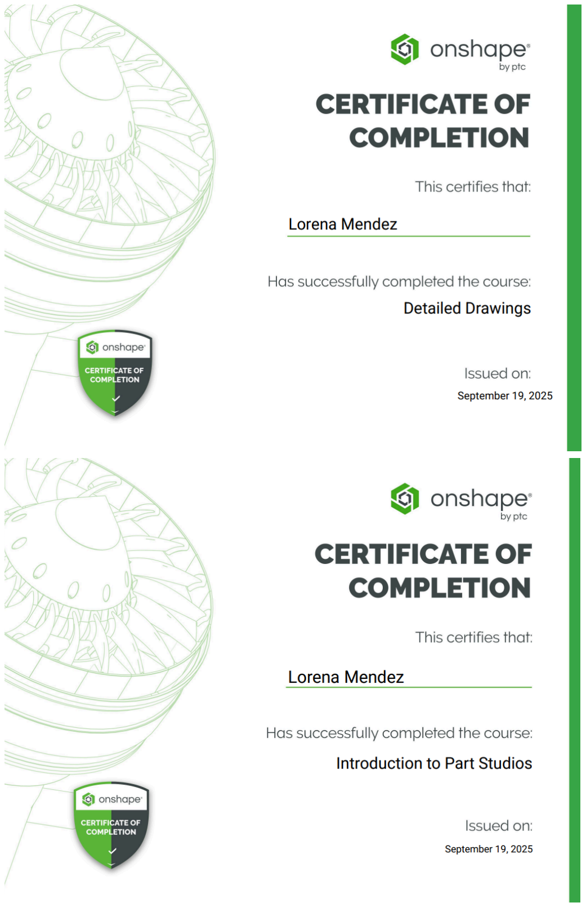
[picture p115: page 1]
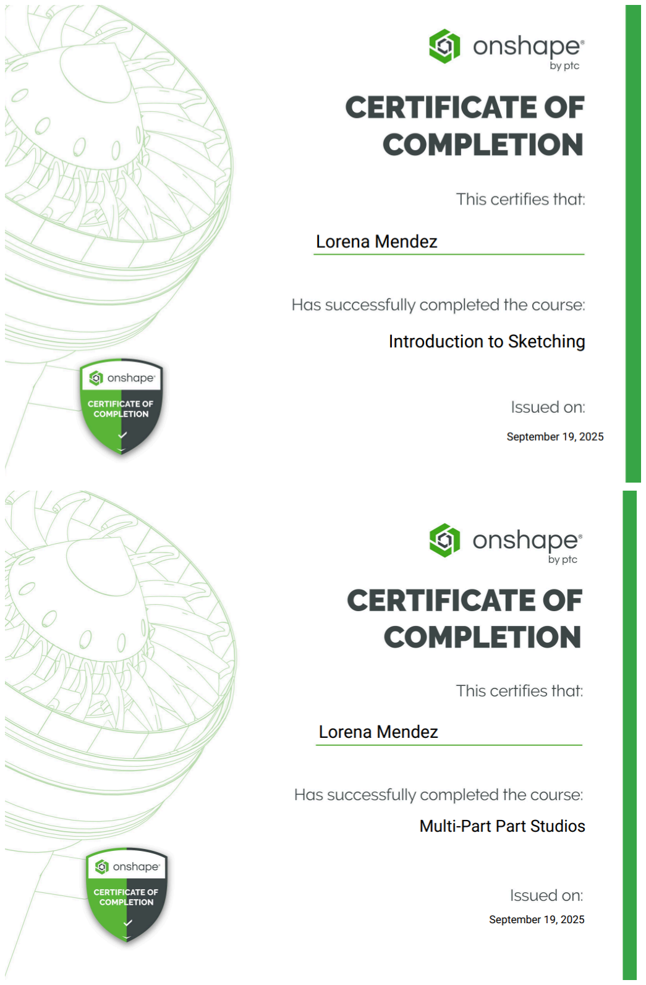
[picture p116: page 2]

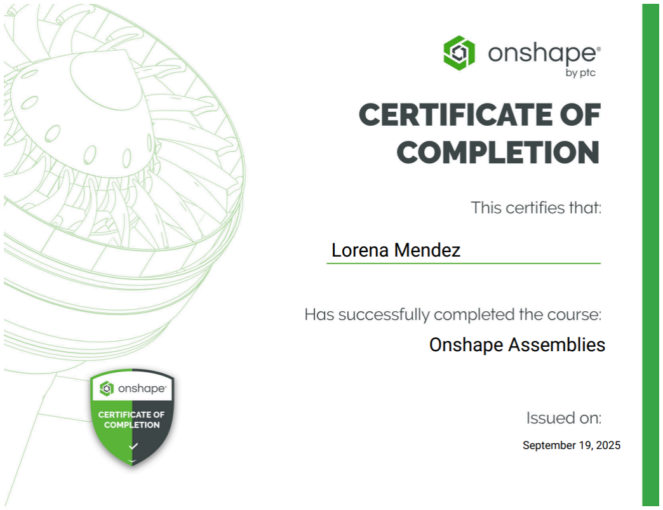
[picture p117: figure]
