juanlugo456/GRUPO-FUNBIO/Talleres/T6/Certificados On Shape de los 5 talleres, Ignacio Pérez Vargas.pdf

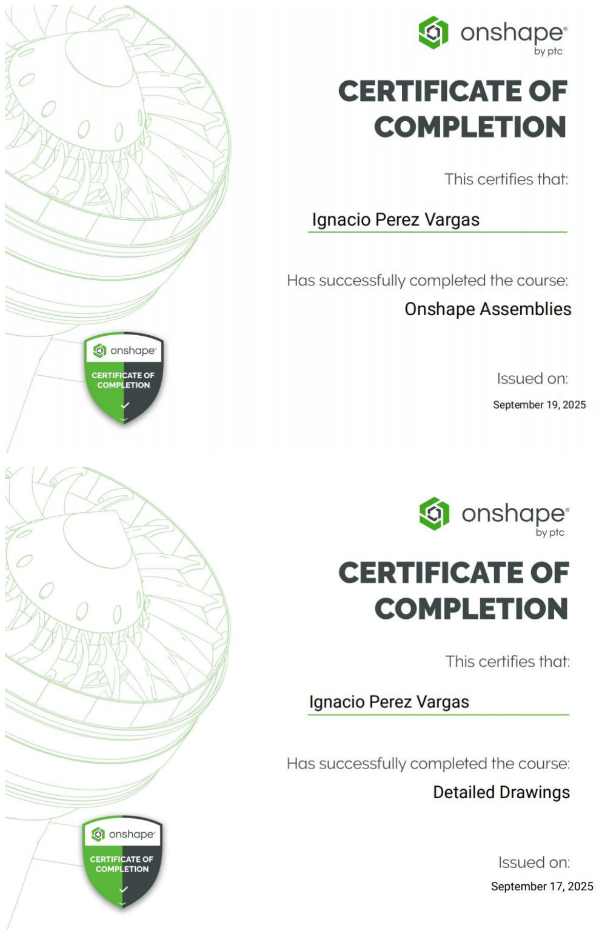
[picture p118: page 1]
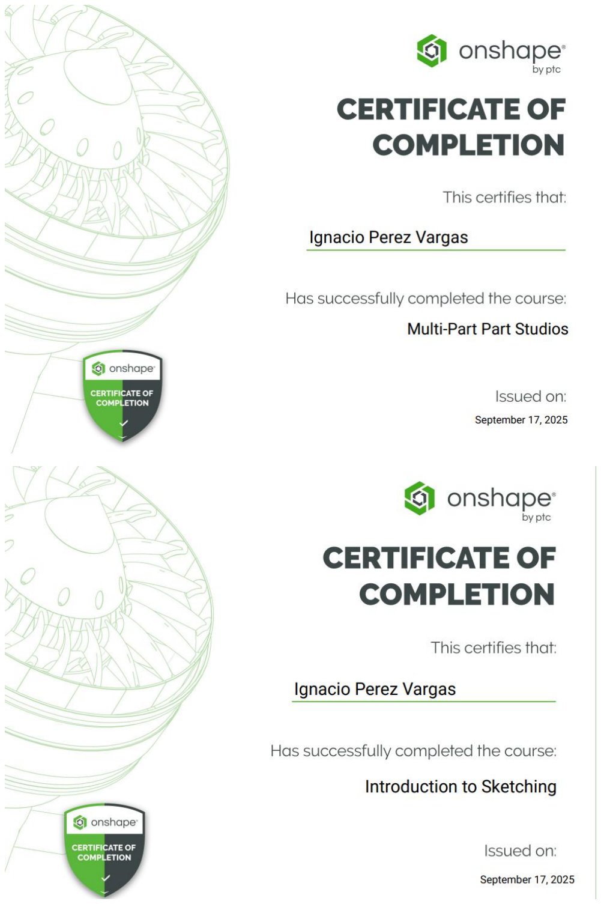
[picture p119: page 2]

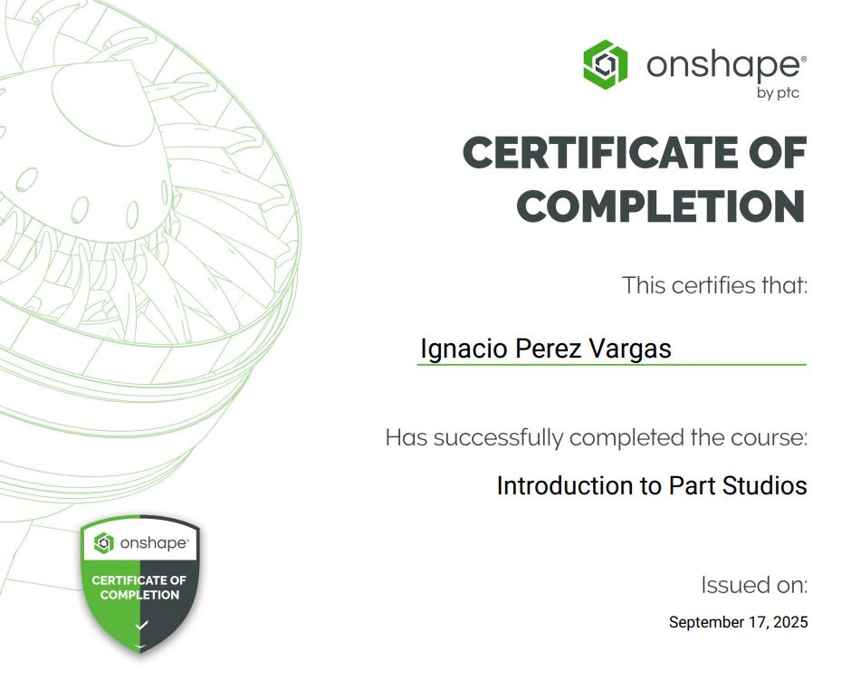
[picture p120: figure]
