juanlugo456/GRUPO-FUNBIO/Talleres/T3/Código2_T2.pdf

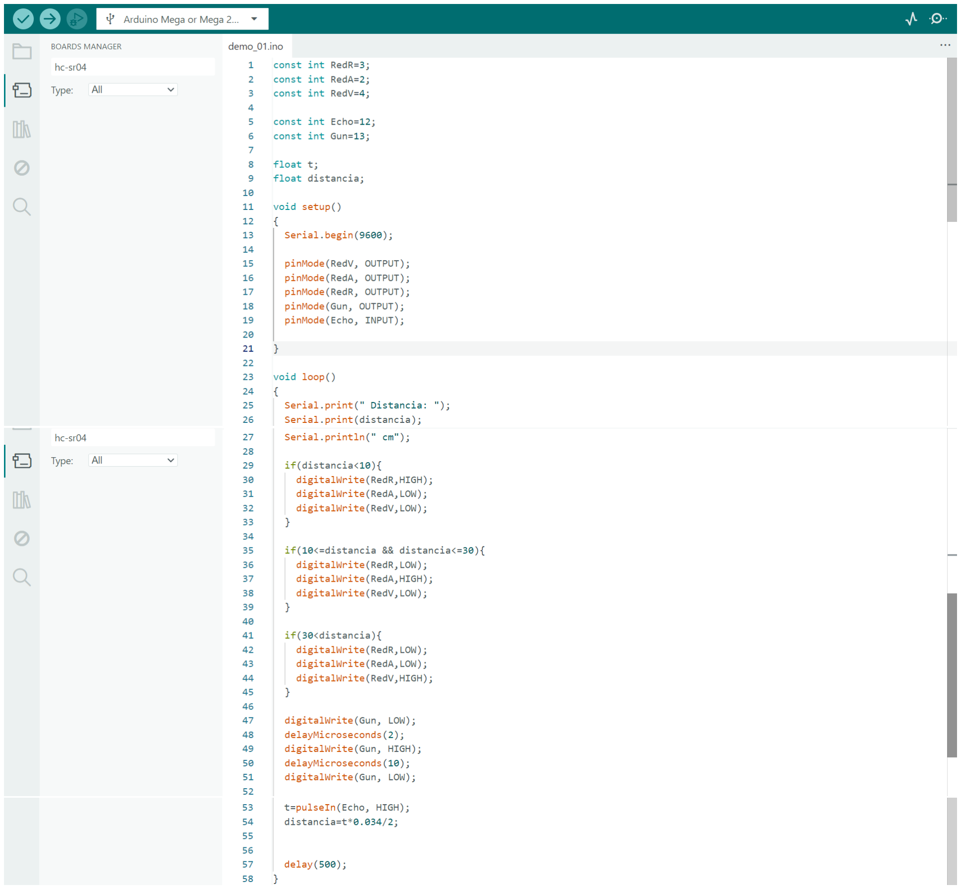
[picture p121: figure]
