juanlugo456/GRUPO-FUNBIO/Talleres/T3/Codigo T1.pdf

Código:

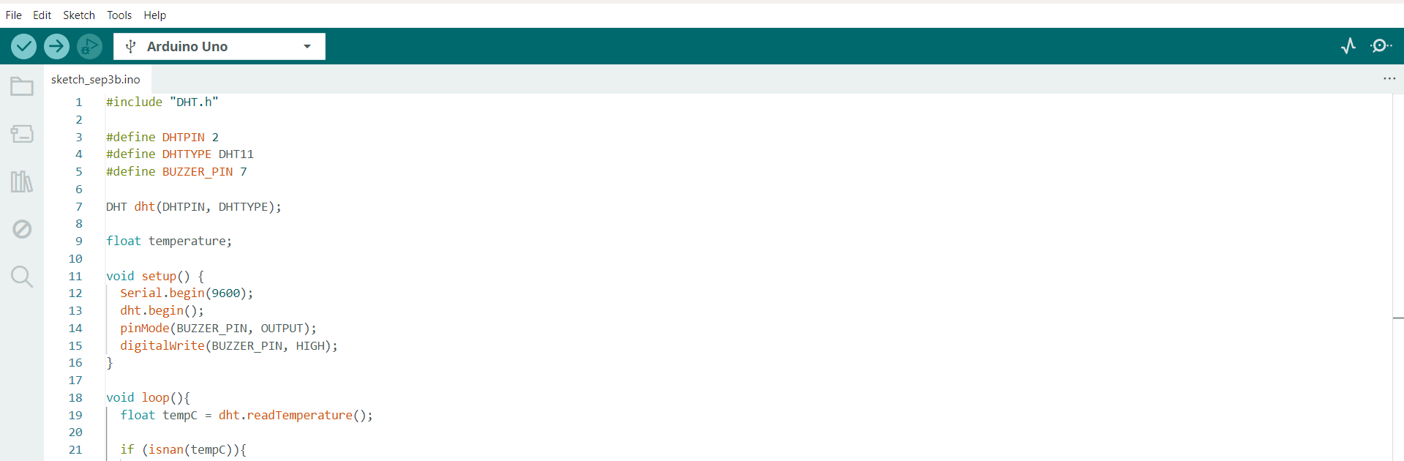
[picture p122: figure]
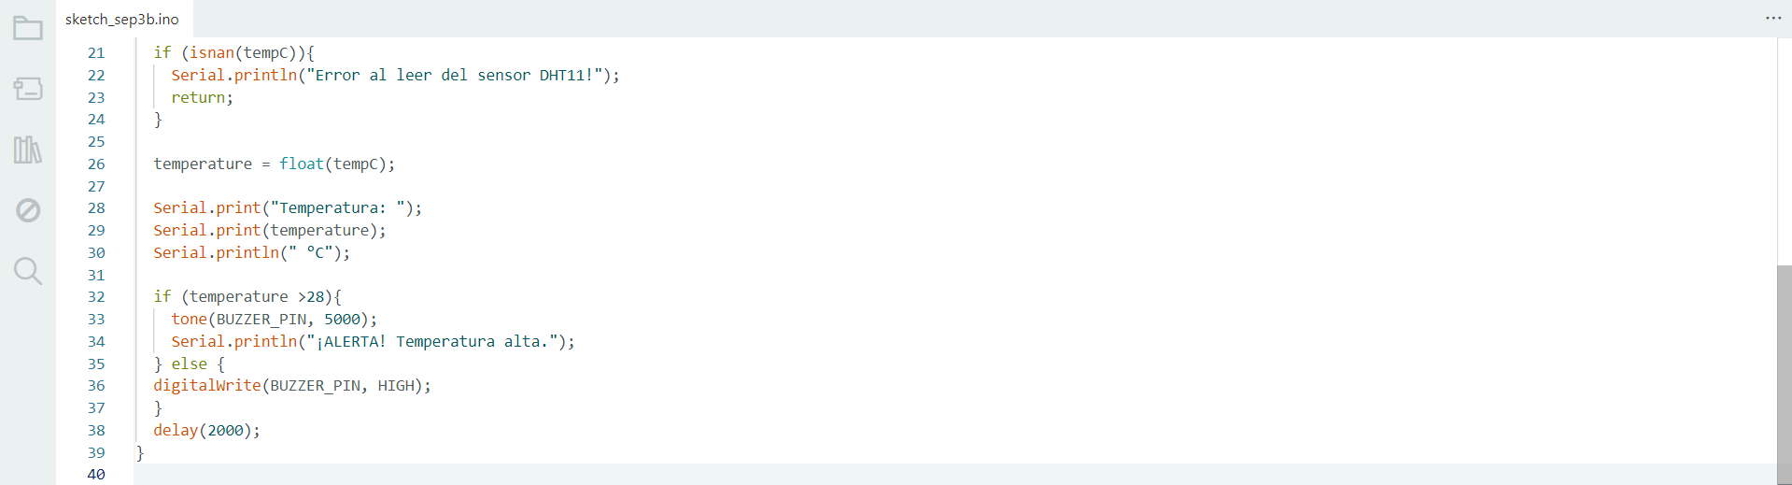
[picture p123: figure]
