juanlugo456/GRUPO-FUNBIO/Talleres/T9/Drive Sleeve Drawing_G1_Grupo3_parte2.pdf

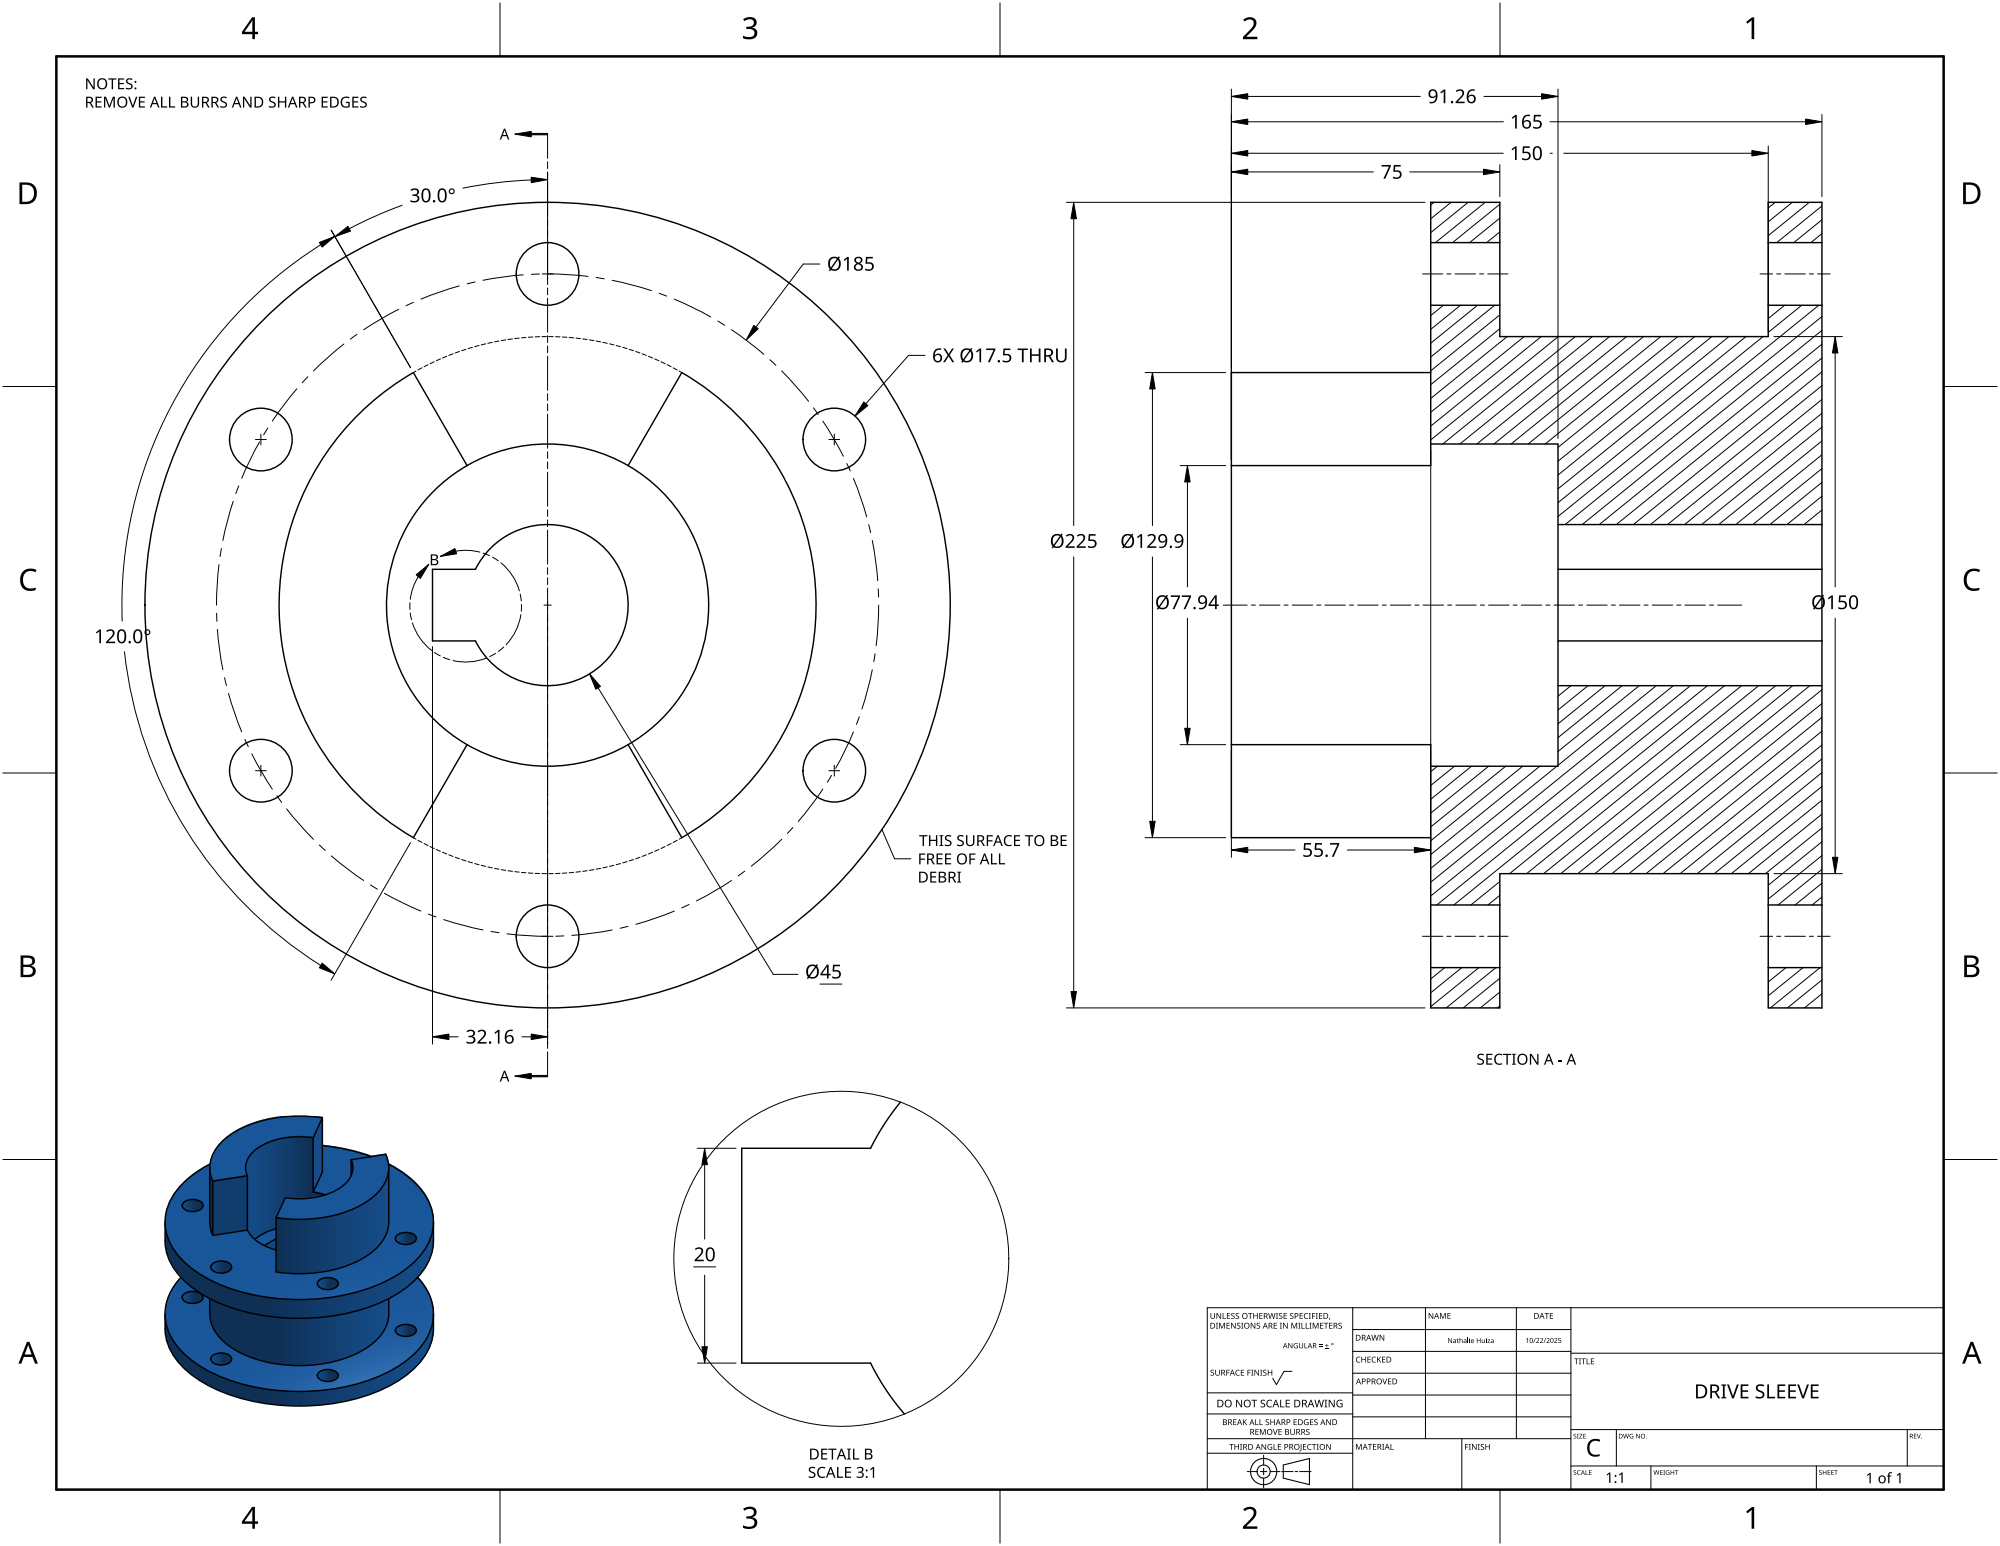
[picture p143: page 1]
