juanlugo456/GRUPO-FUNBIO/Talleres/T9/Universal Joint Flange Drawing (Grupo 3- Horario 1).pdf

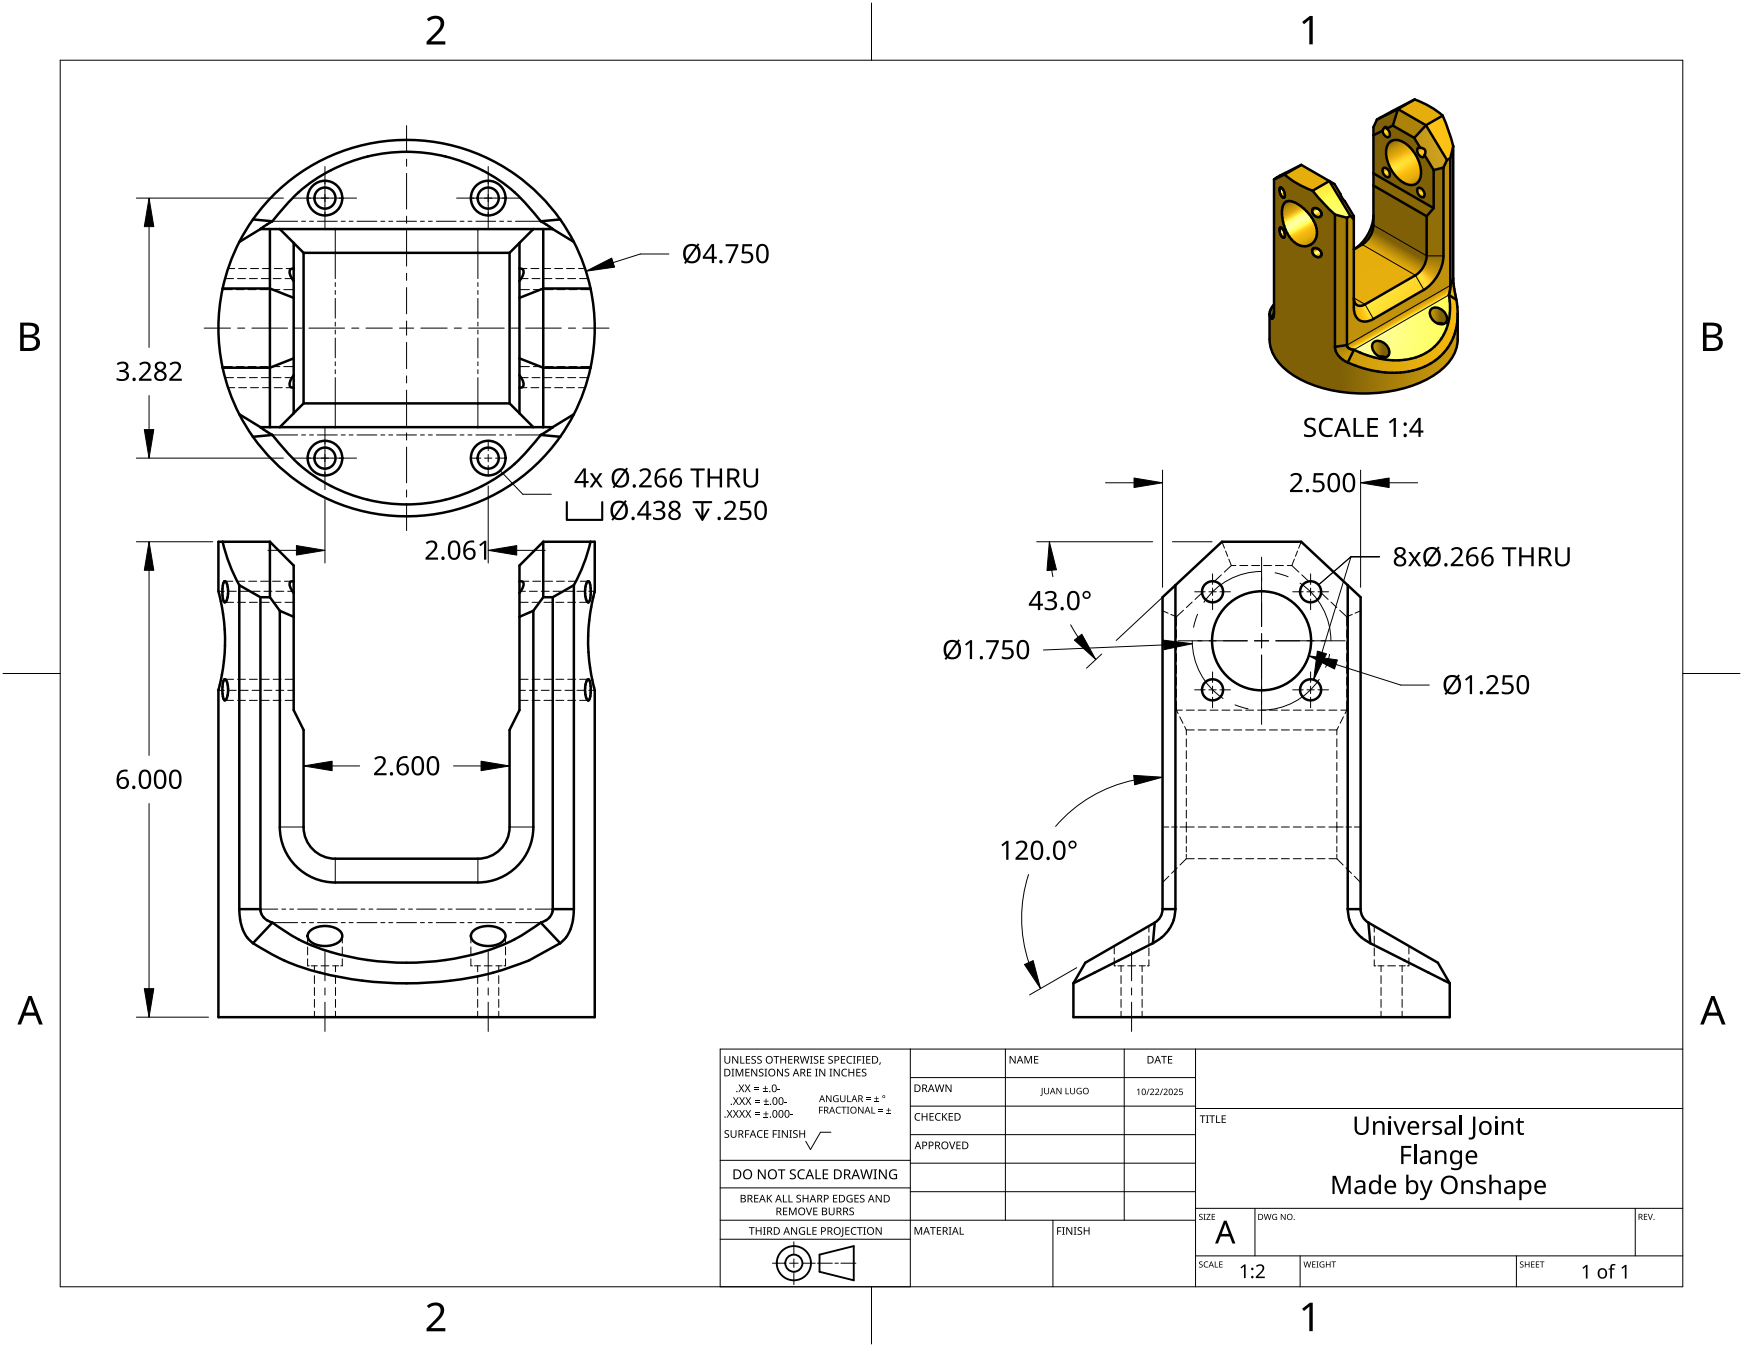
[picture p144: page 1]
